openKolibri/klais-16/docs/char/074.jpg

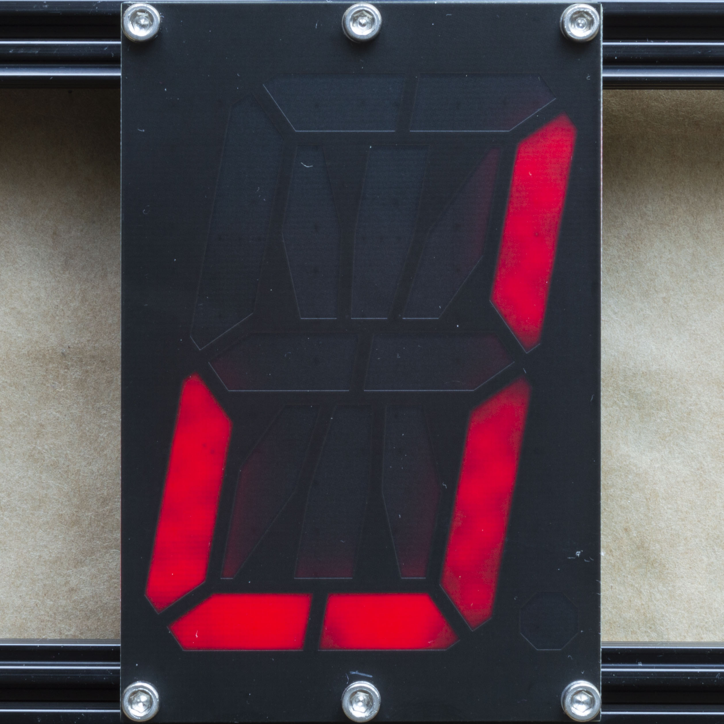
docs/char/074.jpg
