openKolibri/klais-16/docs/char/075.jpg

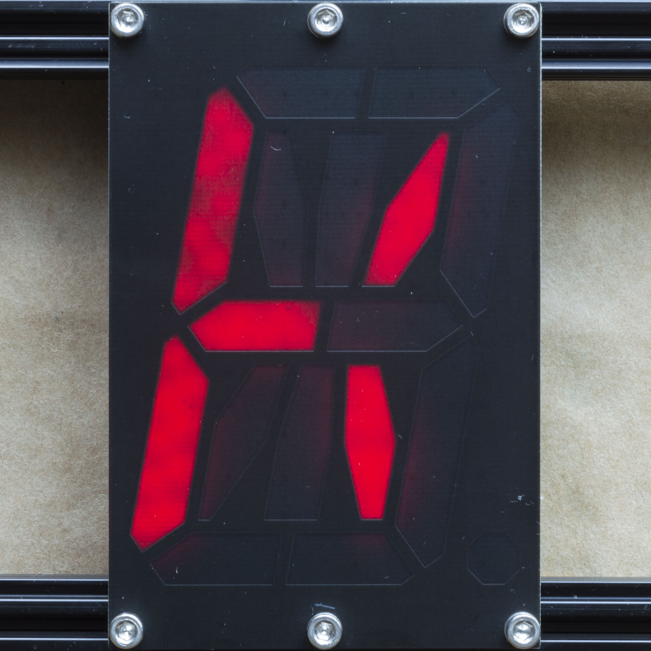
docs/char/075.jpg
