openKolibri/klais-16/docs/char/077.jpg

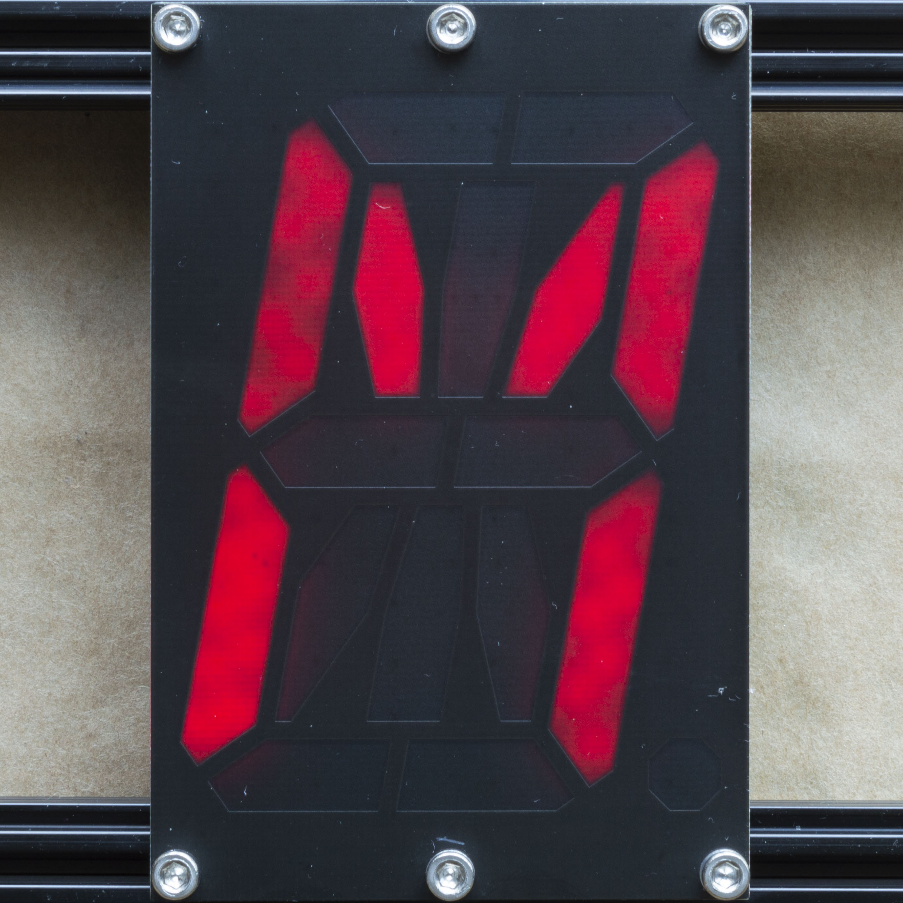
docs/char/077.jpg
