openKolibri/klais-16/docs/char/079.jpg

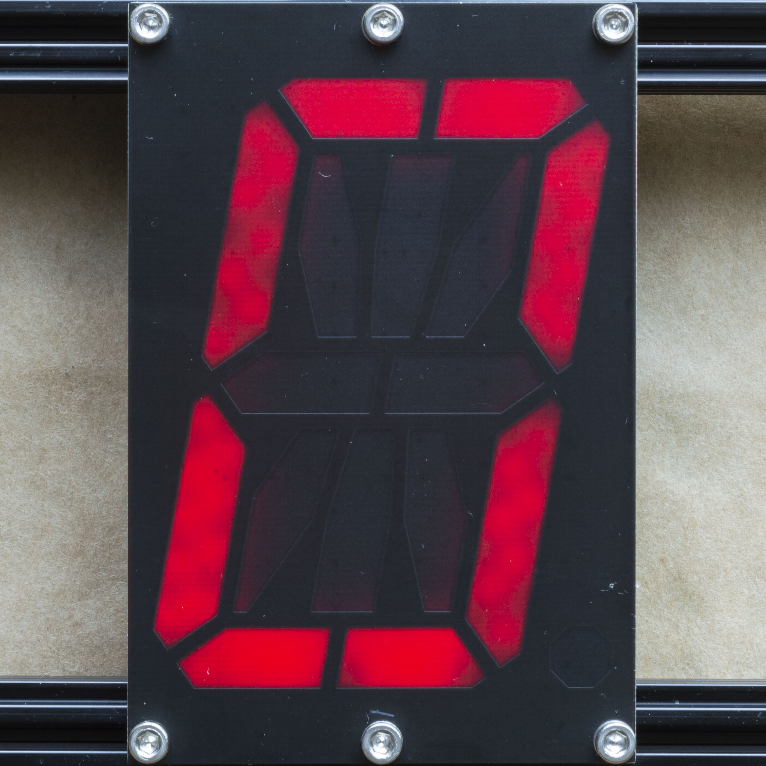
docs/char/079.jpg
