openKolibri/klais-16/docs/char/086.jpg

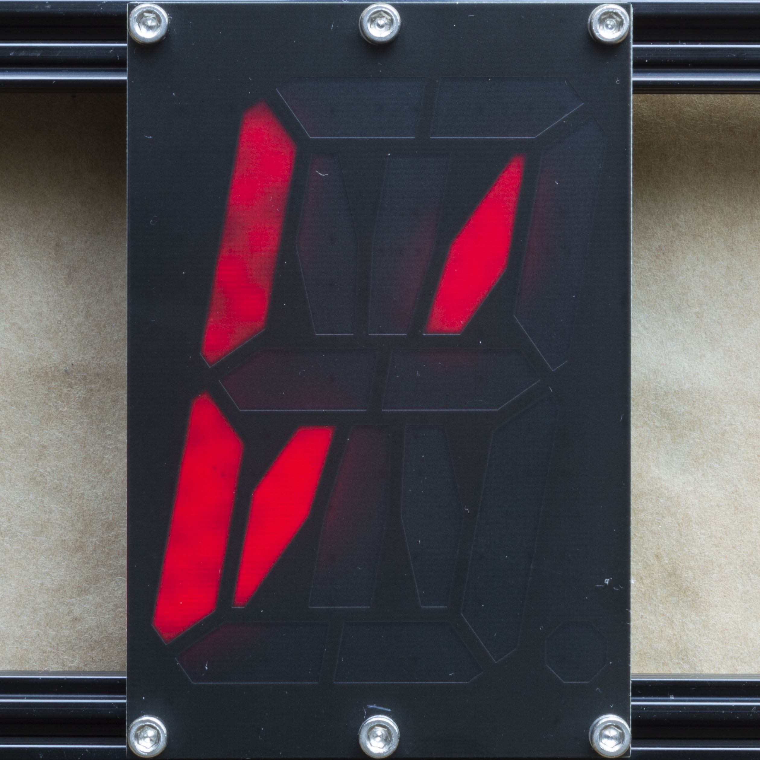
docs/char/086.jpg
