openKolibri/klais-16/docs/char/087.jpg

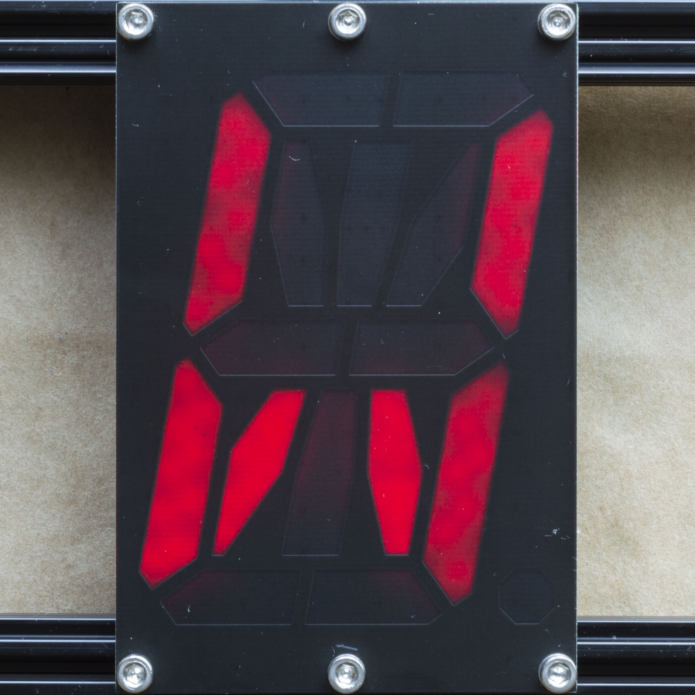
docs/char/087.jpg
