openKolibri/klais-16/docs/char/088.jpg

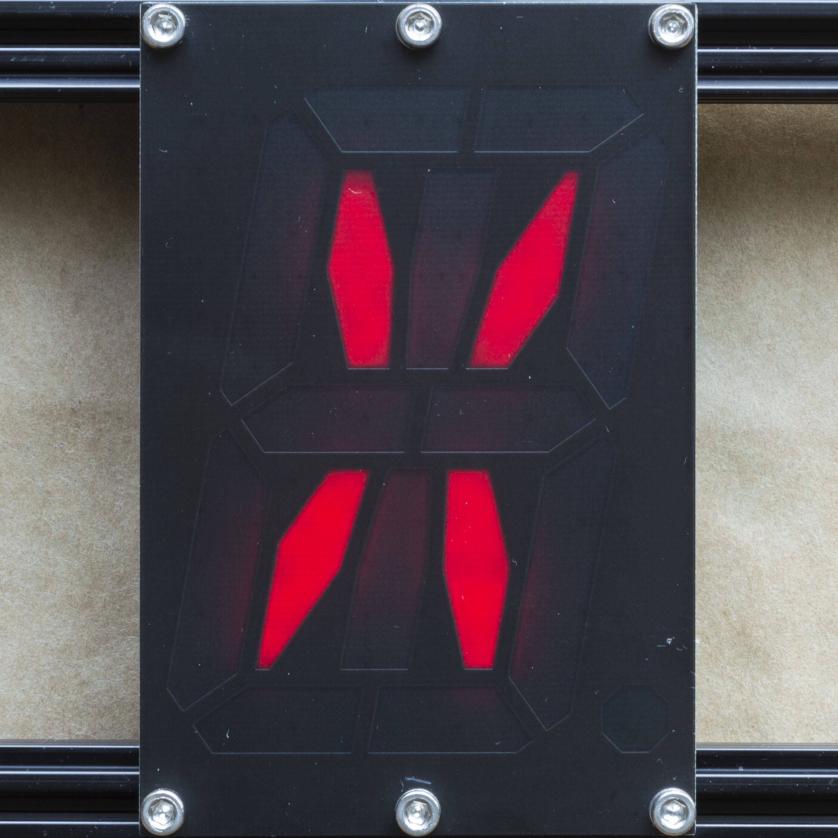
docs/char/088.jpg
