openKolibri/klais-16/docs/char/092.jpg

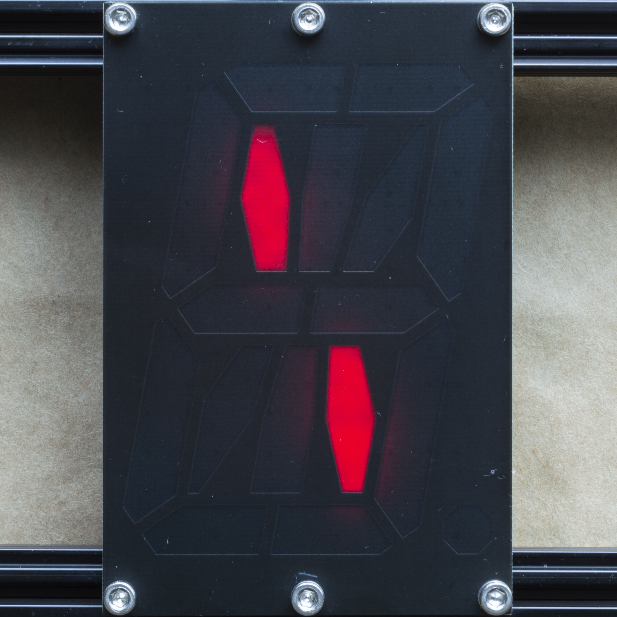
docs/char/092.jpg
