openKolibri/klais-16/docs/char/094.jpg

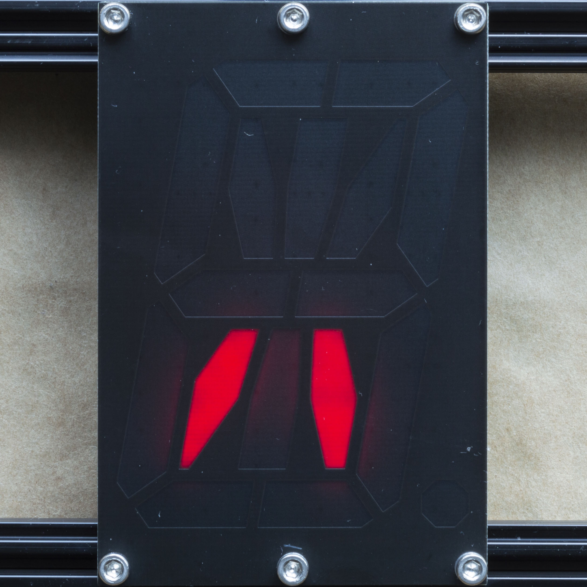
docs/char/094.jpg
