openKolibri/klais-16/docs/char/096.jpg

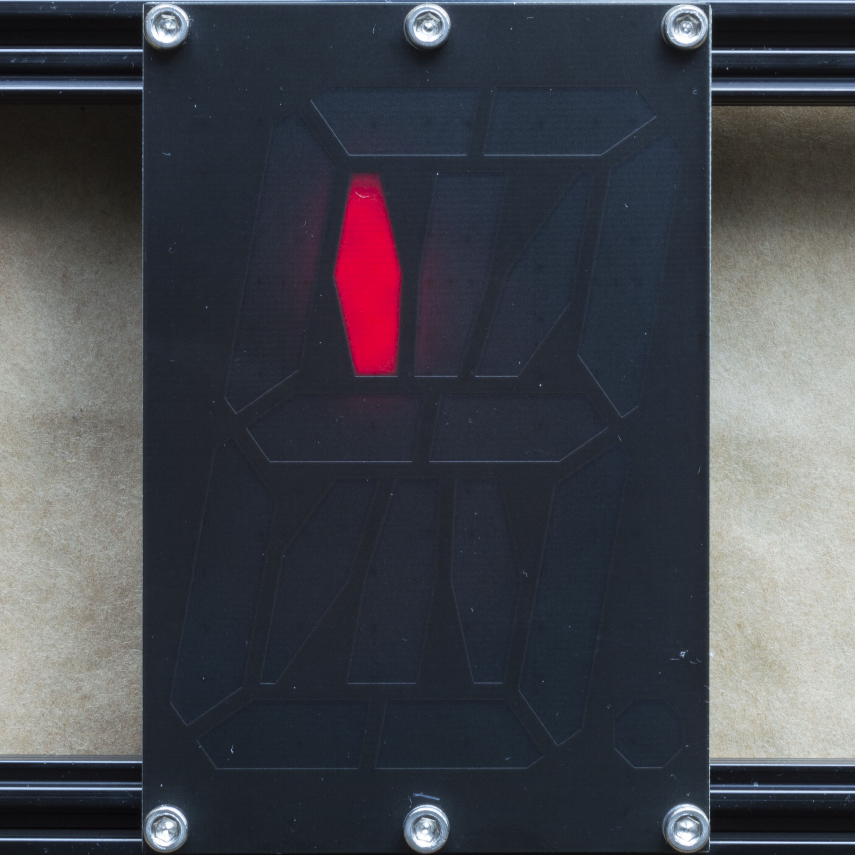
docs/char/096.jpg
