openKolibri/klais-16/docs/char/097.jpg

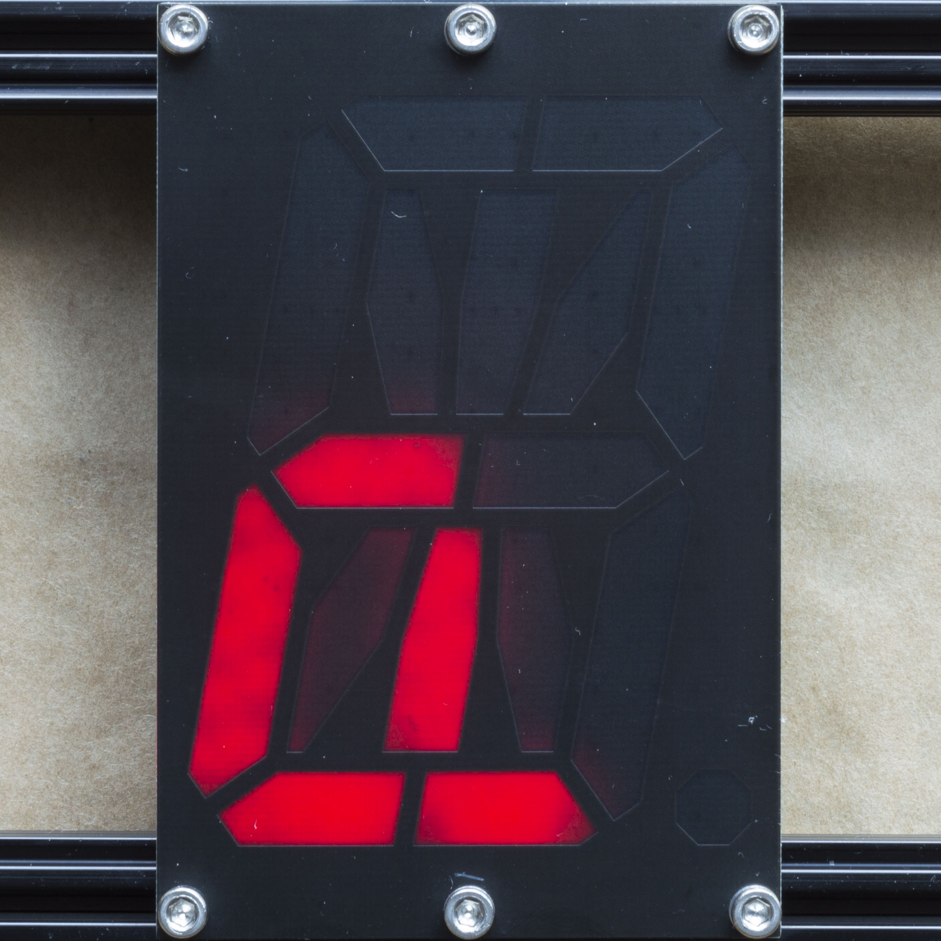
docs/char/097.jpg
