openKolibri/klais-16/docs/char/098.jpg

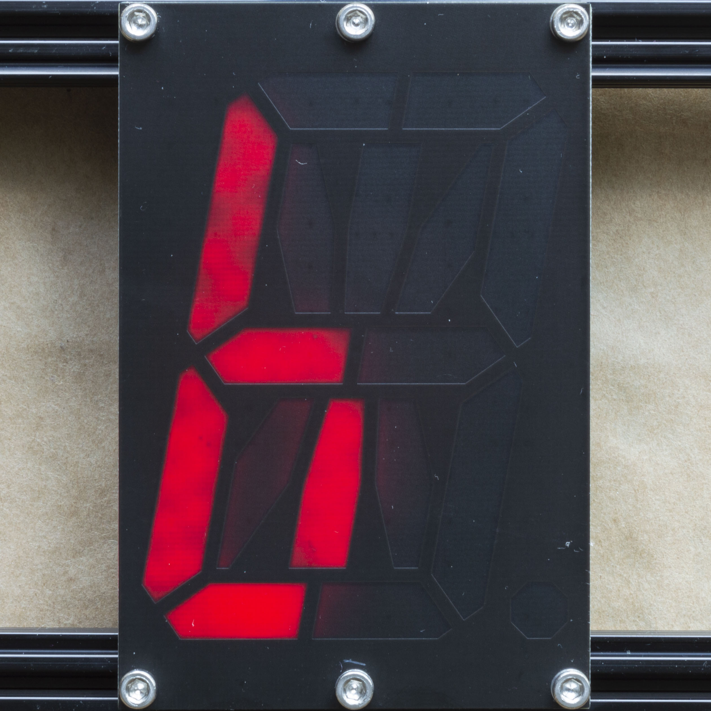
docs/char/098.jpg
