openKolibri/klais-16/docs/char/101.jpg

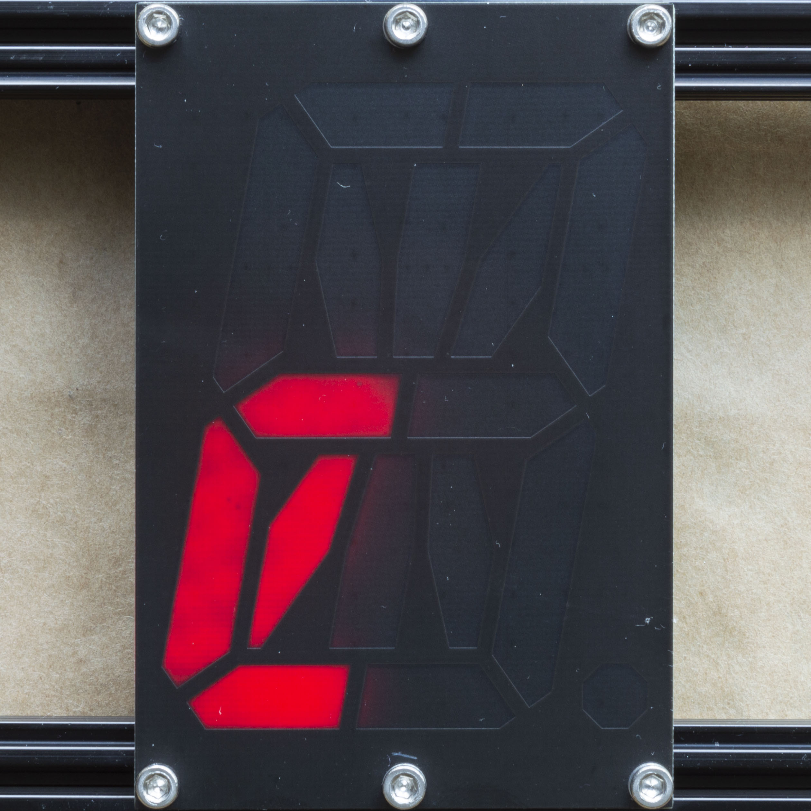
docs/char/101.jpg
