openKolibri/klais-16/docs/char/106.jpg

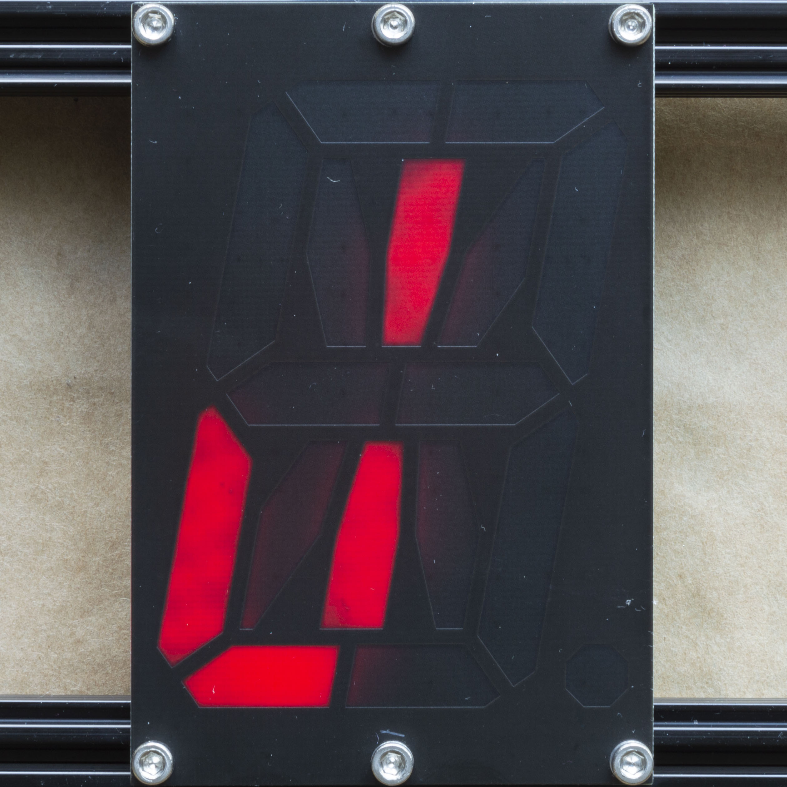
docs/char/106.jpg
