openKolibri/klais-16/docs/char/108.jpg

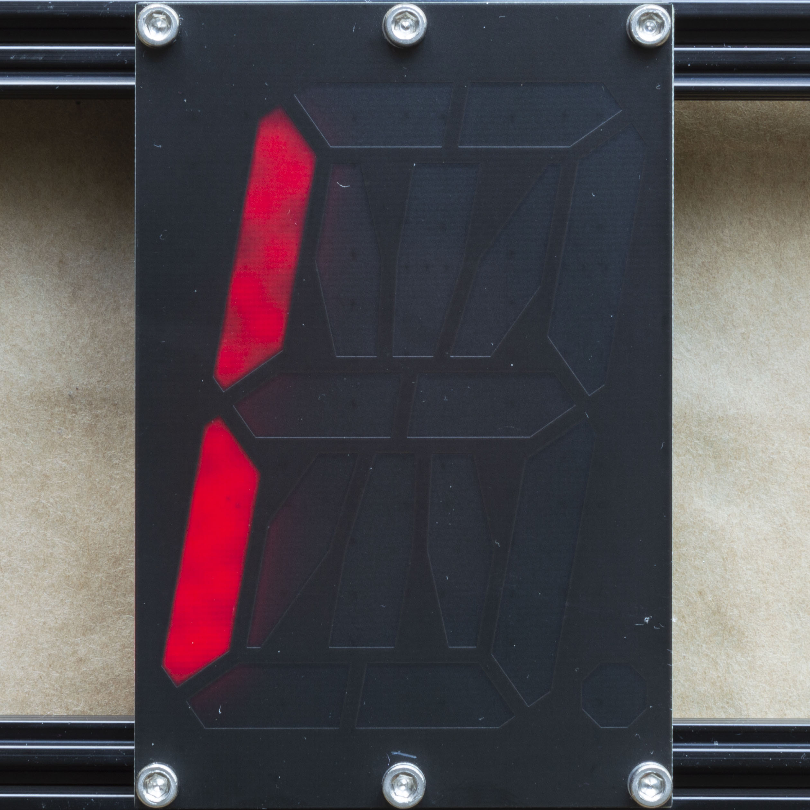
docs/char/108.jpg
