openKolibri/klais-16/docs/char/109.jpg

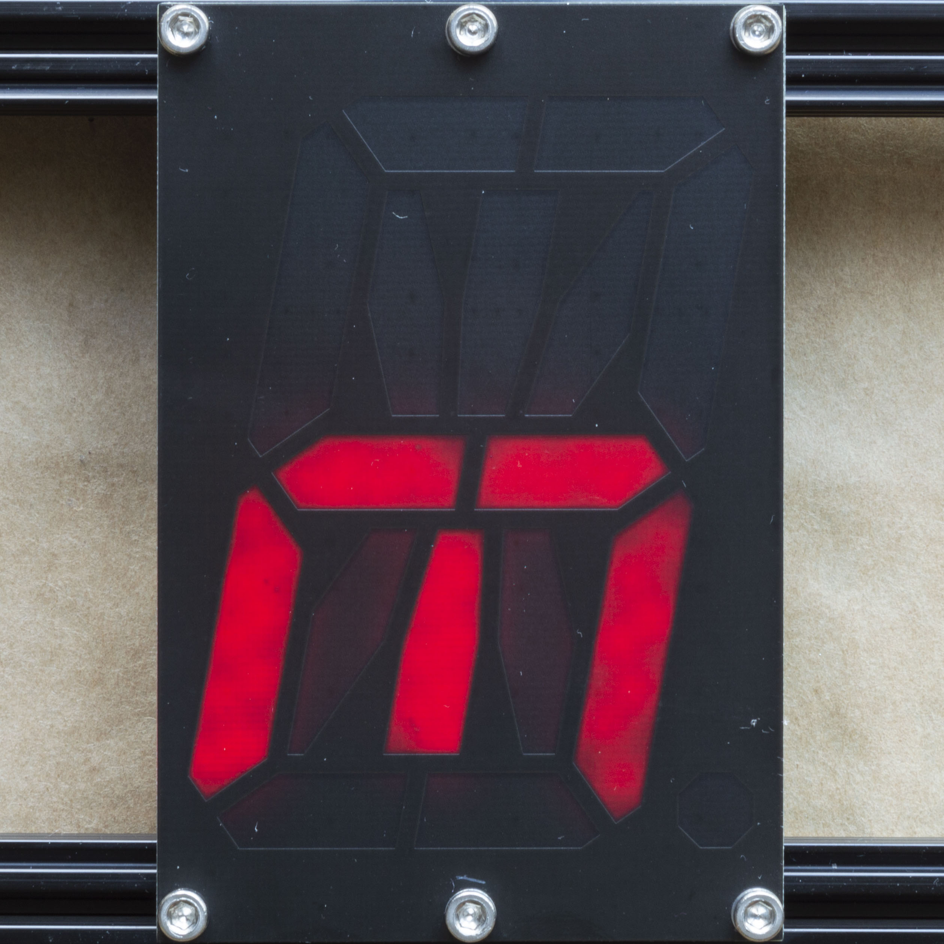
docs/char/109.jpg
