openKolibri/klais-16/docs/char/114.jpg

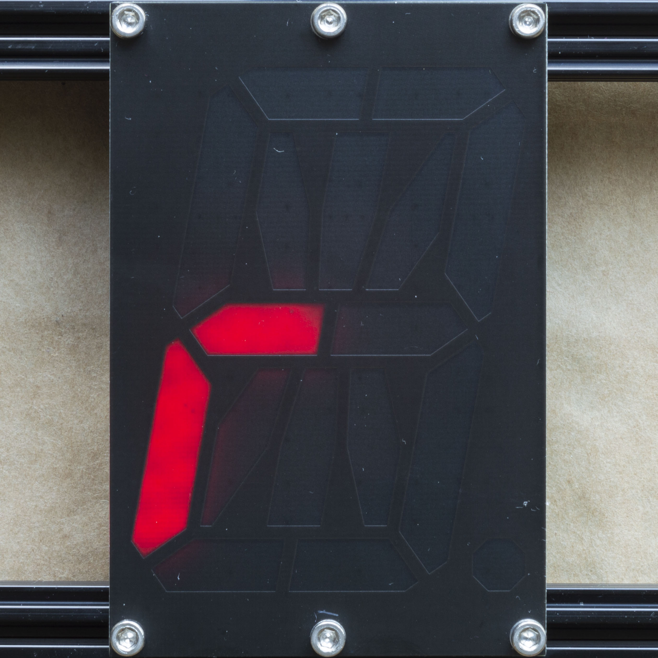
docs/char/114.jpg
