openKolibri/klais-16/docs/char/115.jpg

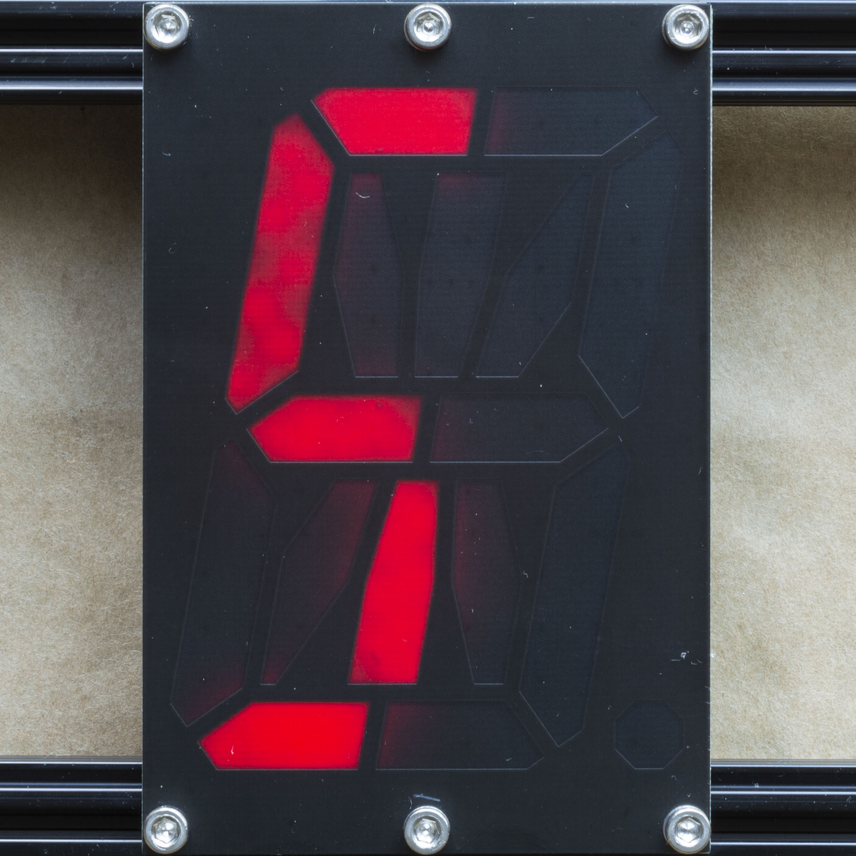
docs/char/115.jpg
