openKolibri/klais-16/docs/char/119.jpg

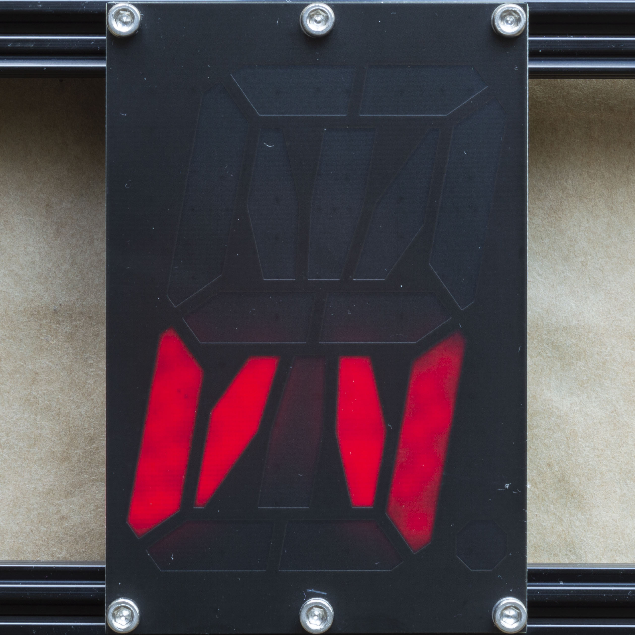
docs/char/119.jpg
