openKolibri/klais-16/docs/char/126.jpg

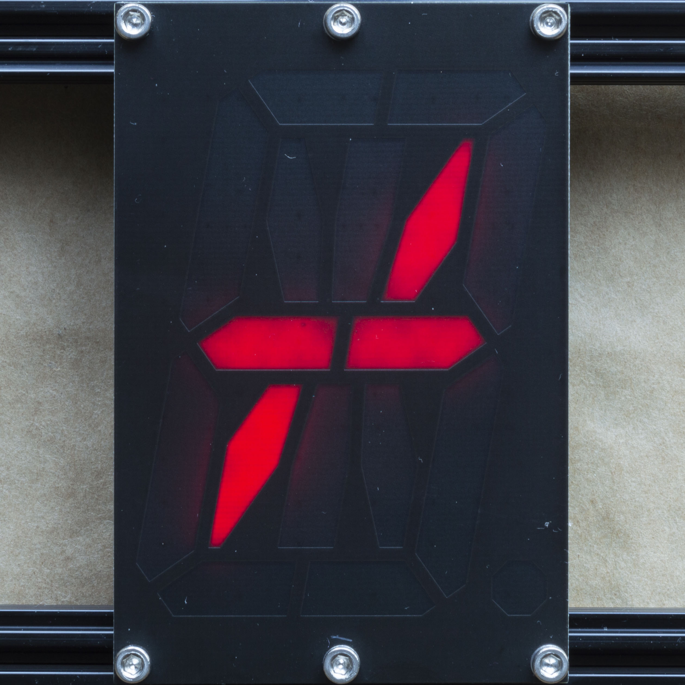
docs/char/126.jpg
