openKolibri/klais-16/docs/config/backPanel.jpg

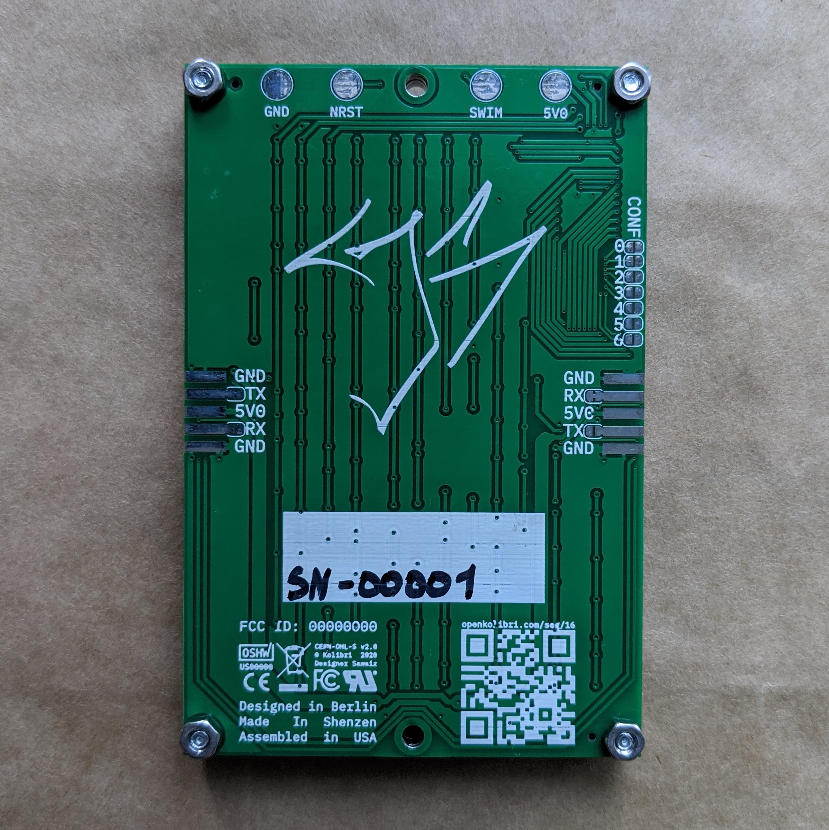
docs/config/backPanel.jpg
