openKolibri/klais-16/docs/config/config.jpg

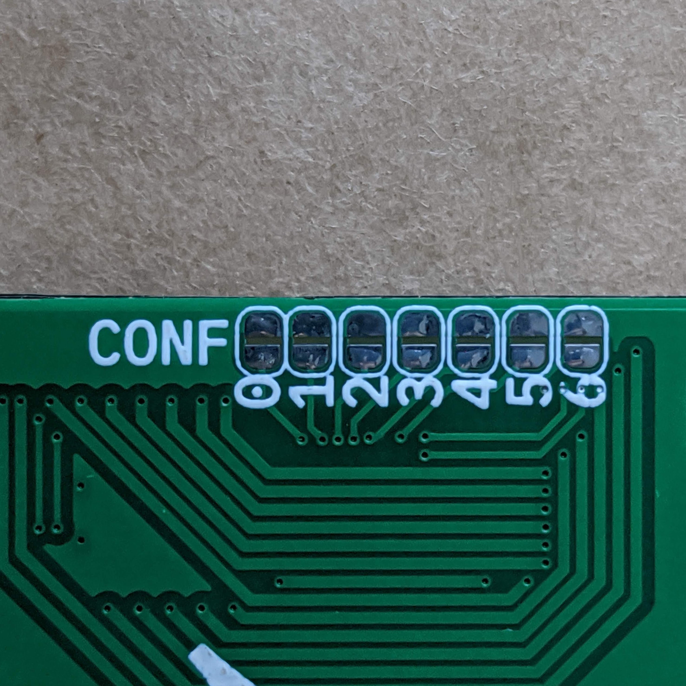
docs/config/config.jpg
