openKolibri/klais-16/docs/config/keyed.jpg

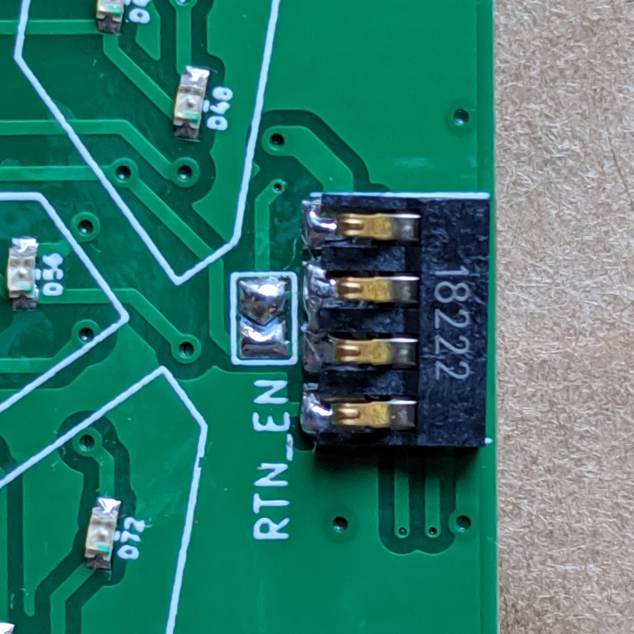
docs/config/keyed.jpg
