openKolibri/klais-16/docs/config/label.png

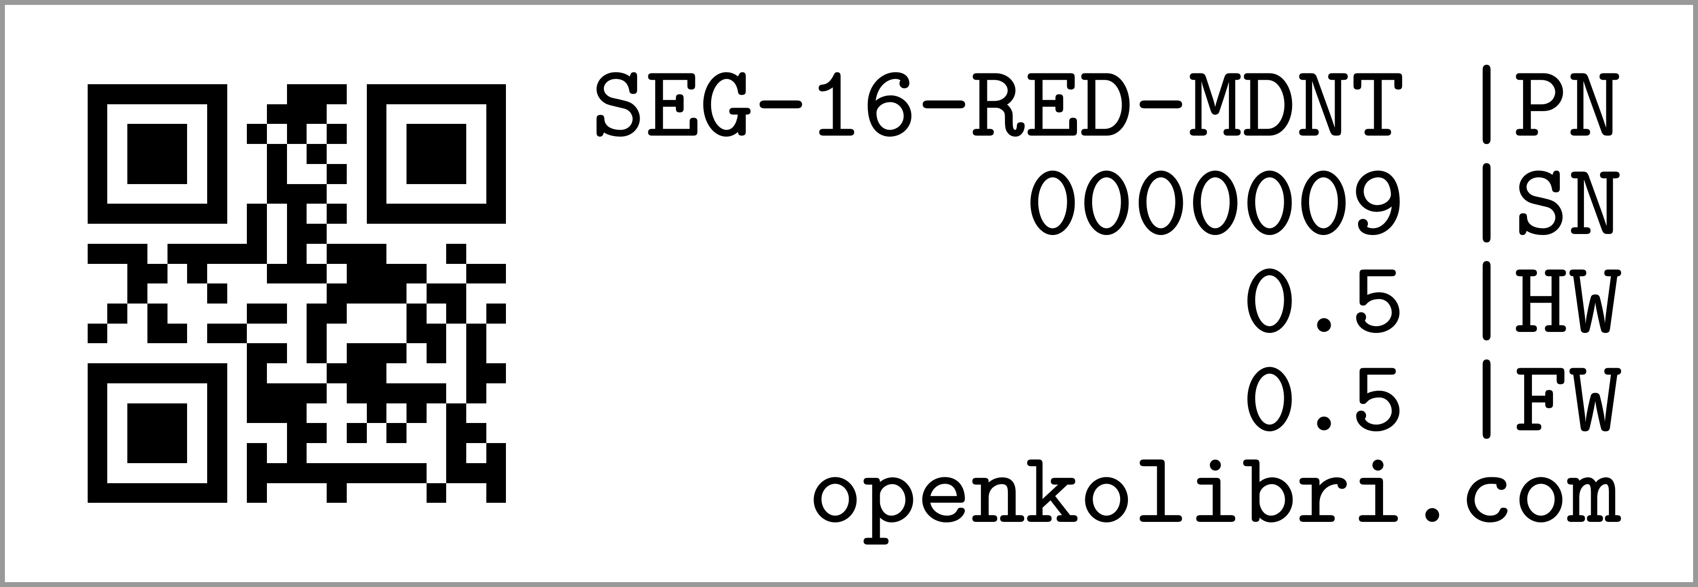
docs/config/label.png
