openKolibri/klais-16/docs/config/pgrm.jpg

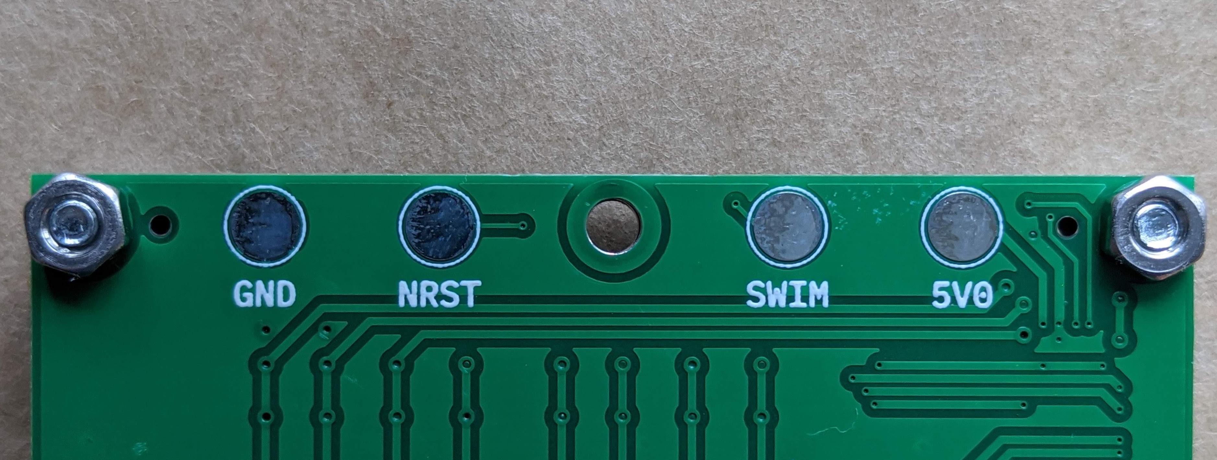
docs/config/pgrm.jpg
