openKolibri/klais-16/docs/firmware/dataCapImg.png

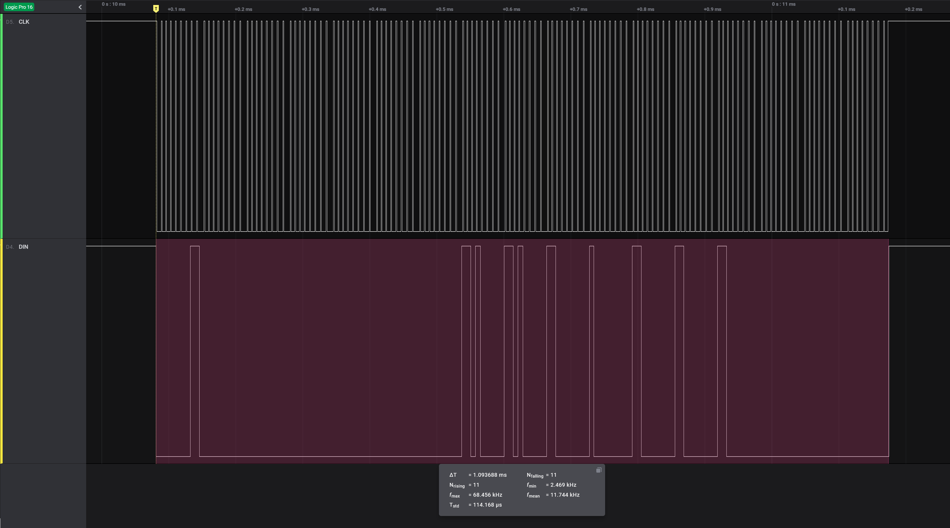
docs/firmware/dataCapImg.png
