openKolibri/klais-16/docs/firmware/segmentMap.png

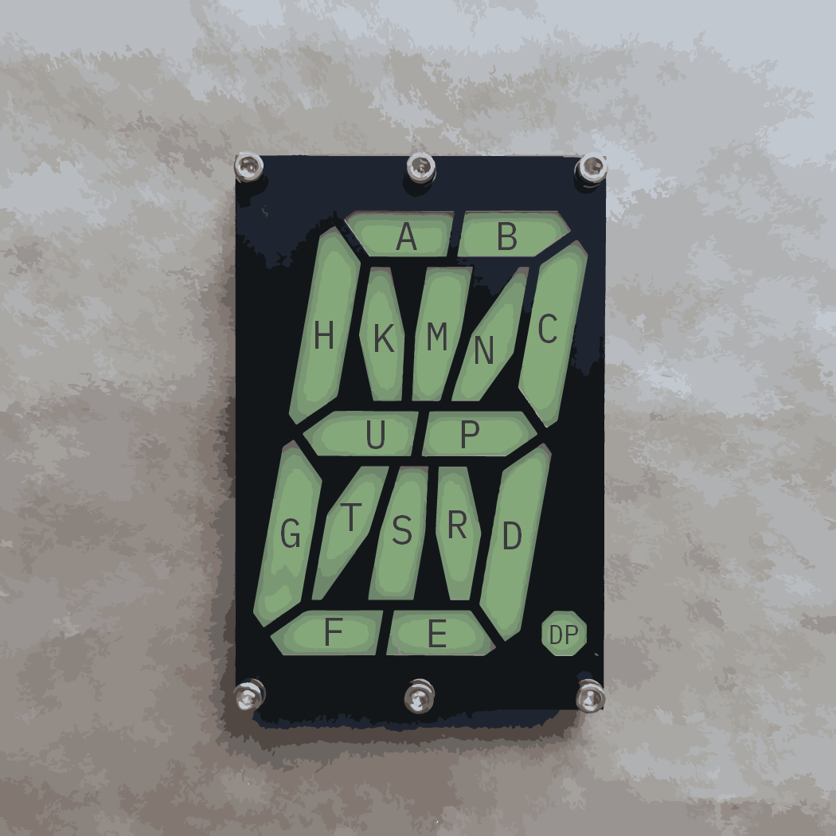
docs/firmware/segmentMap.png
