openKolibri/klais-16/docs/firmware/TM1640Timing.png

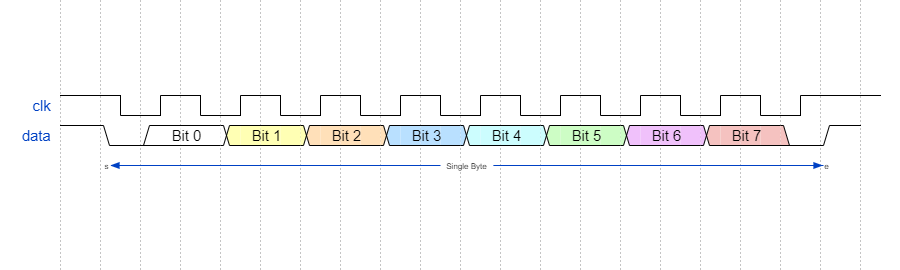
docs/firmware/TM1640Timing.png
