openKolibri/klais-16/docs/mounting/2020Extrusion.jpg

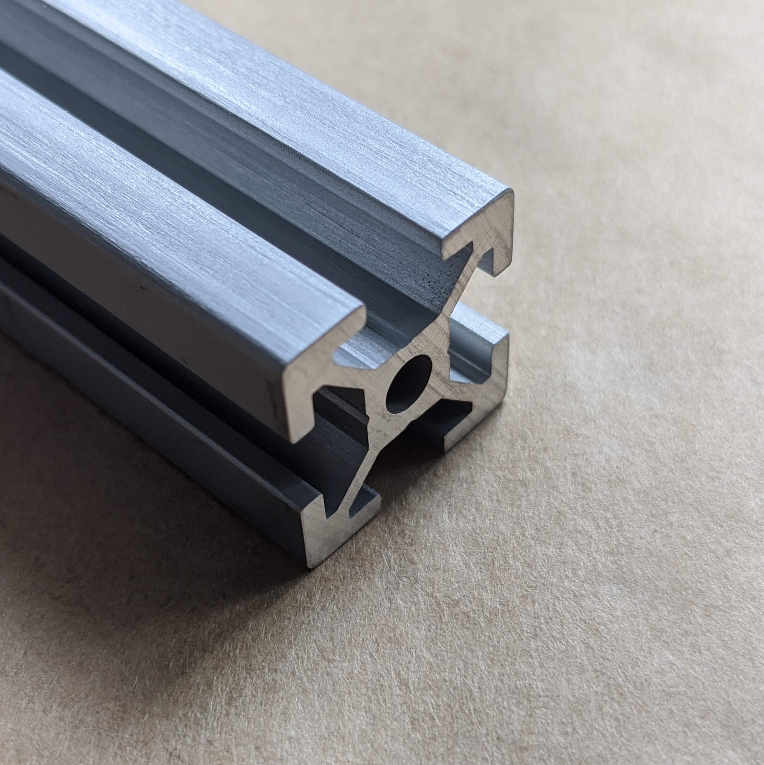
docs/mounting/2020Extrusion.jpg
