openKolibri/klais-16/docs/mounting/M3x8.jpg

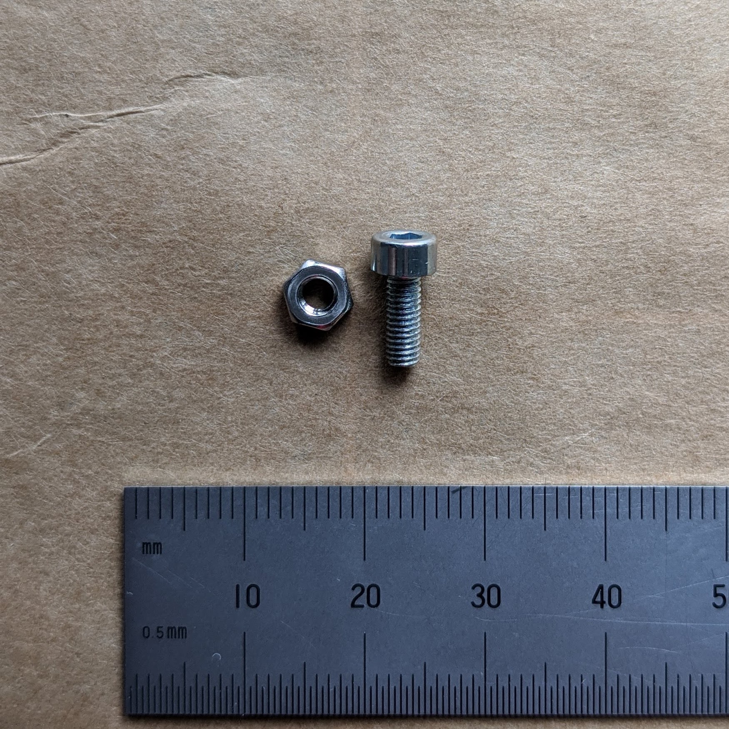
docs/mounting/M3x8.jpg
