openKolibri/klais-16/docs/mounting/mountingDim.png

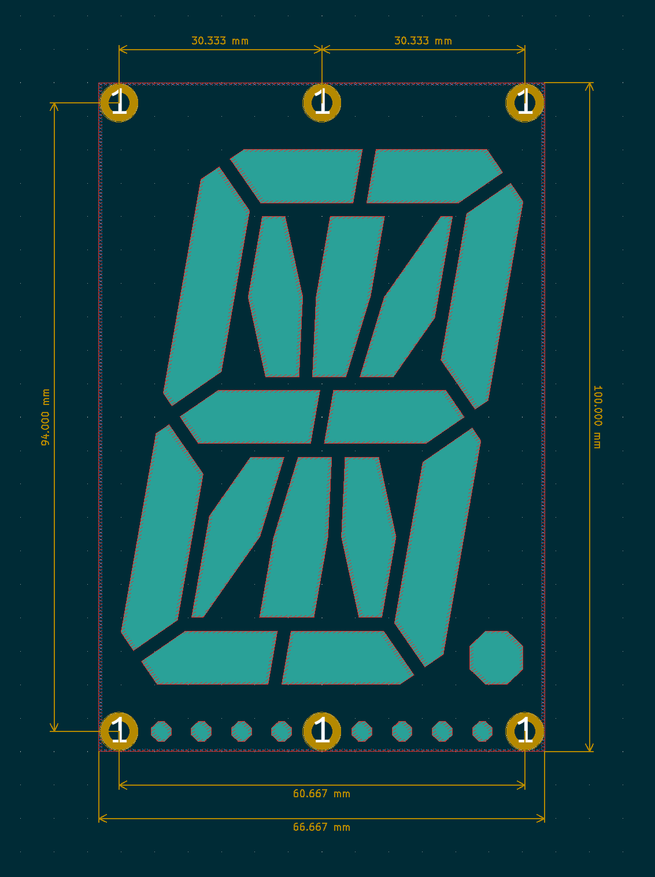
docs/mounting/mountingDim.png
