openKolibri/klais-16/docs/mounting/R3075.jpg

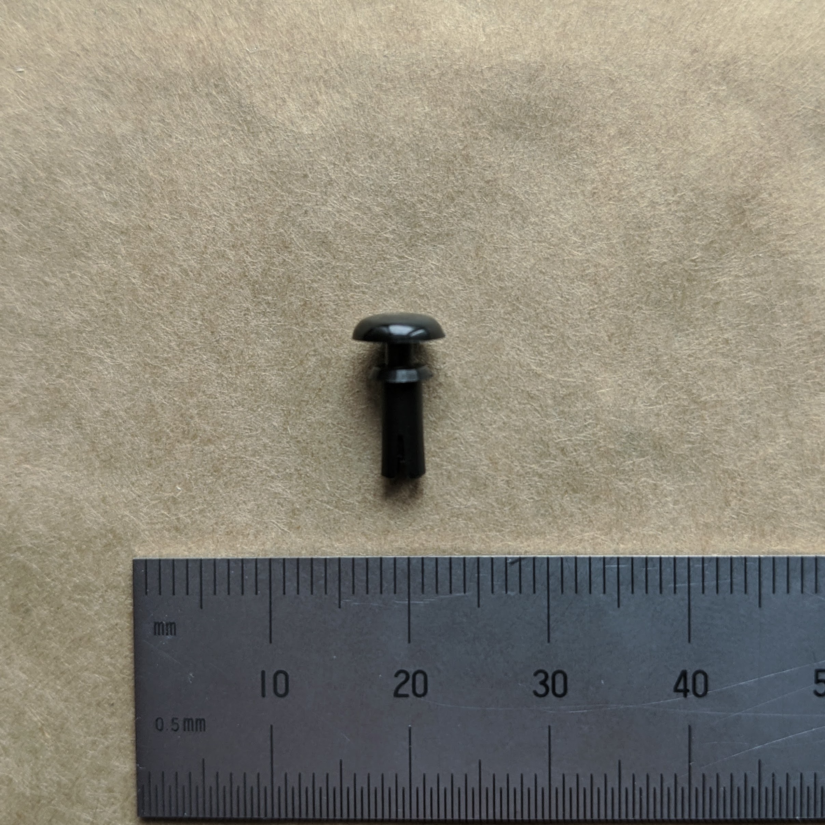
docs/mounting/R3075.jpg
