openKolibri/klais-16/docs/mounting/springPin.jpg

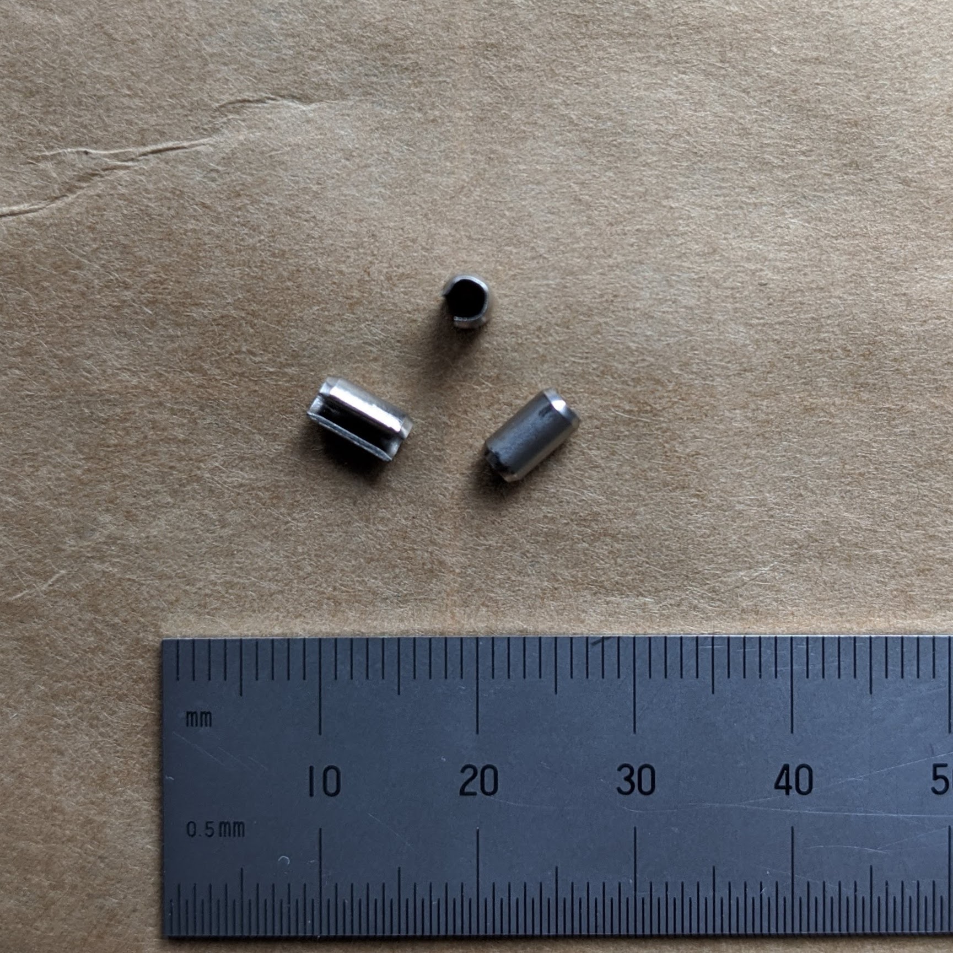
docs/mounting/springPin.jpg
