openKolibri/klais-16/docs/product/isoArray.jpg

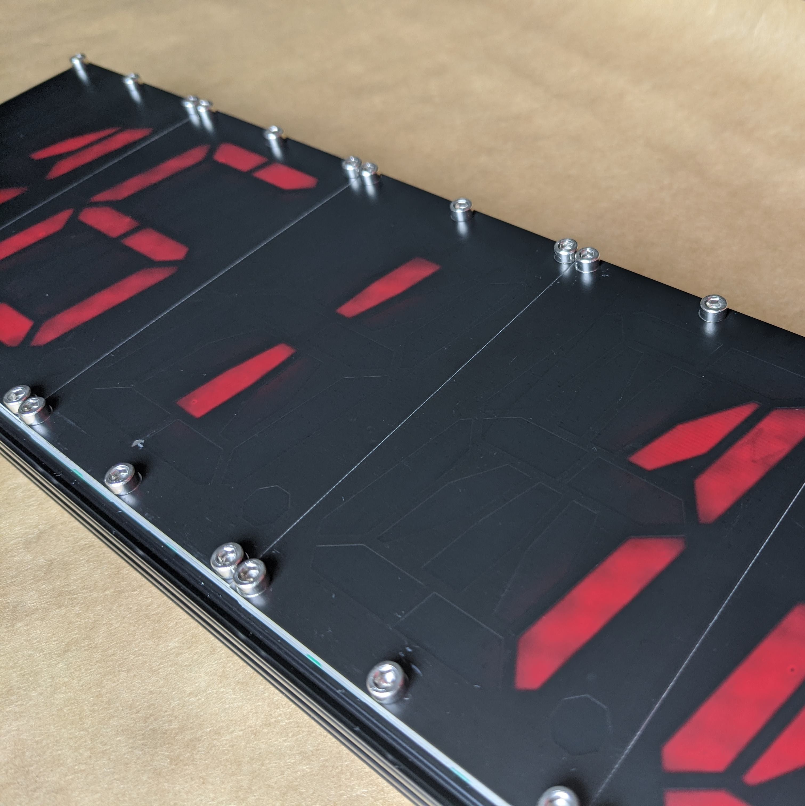
docs/product/isoArray.jpg
