openKolibri/klais-16/docs/programmer/minimalProgrammer-render.png

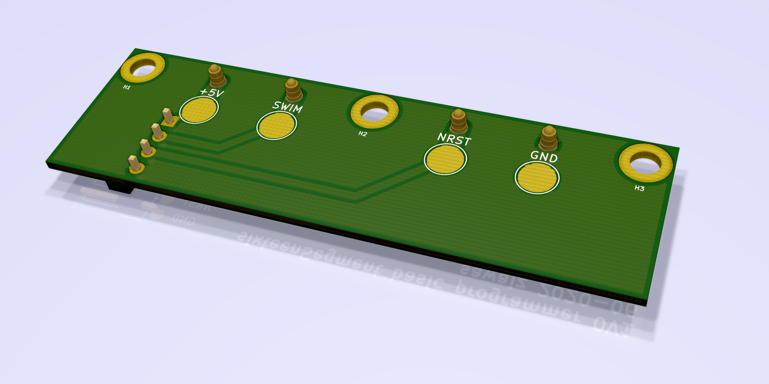
docs/programmer/minimalProgrammer-render.png
