openKolibri/klais-16/docs/title/DISPLAY.png

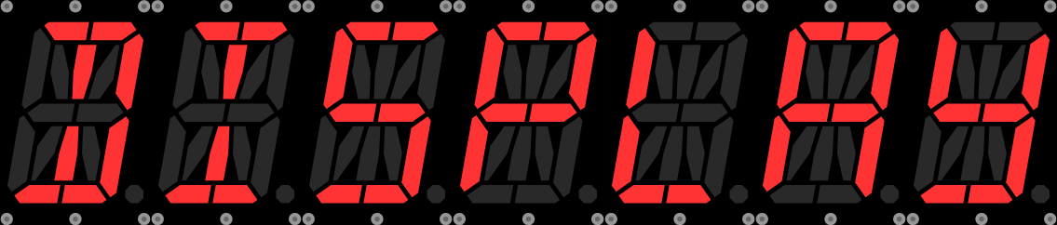
docs/title/DISPLAY.png
