openKolibri/klais-16/docs/title/SEGMENT.png

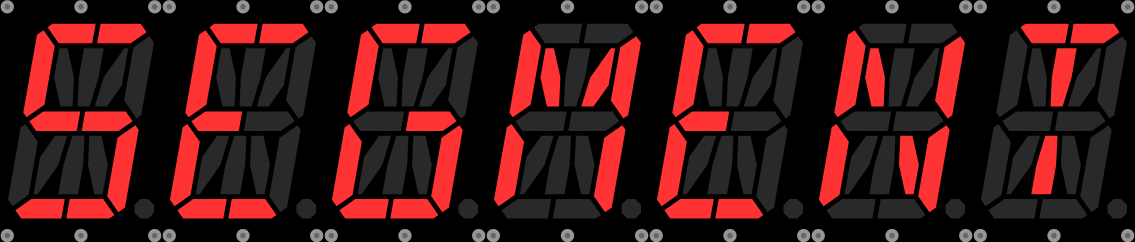
docs/title/SEGMENT.png
