openKolibri/klais-16/docs/title/SIXTEEN.png

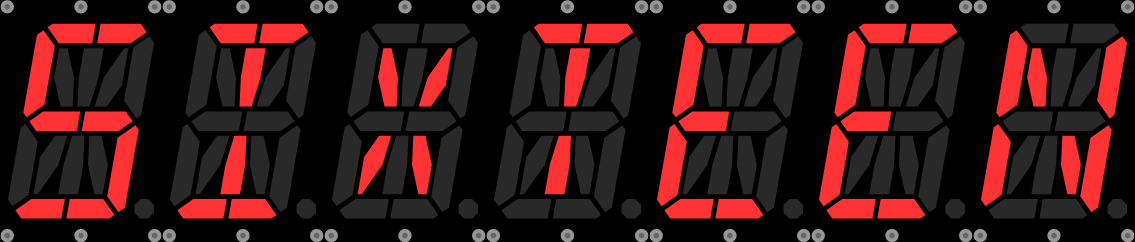
docs/title/SIXTEEN.png
