openKolibri/klais-16/pcb/SEG-16-XXX-XXXX-L0/components/0472861001/0472861001.jpg

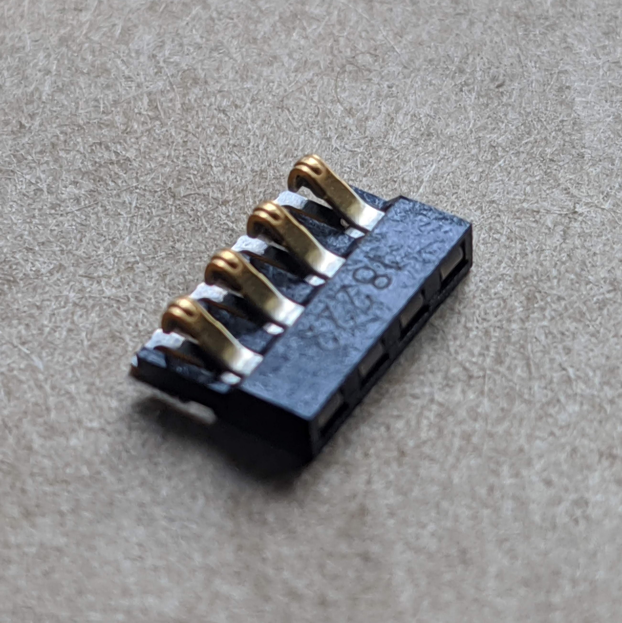
pcb/SEG-16-XXX-XXXX-L0/components/0472861001/0472861001.jpg
