openKolibri/klais-16/pcb/SEG-16-XXX-XXXX-L0/components/KT-0603R/KT-0603R.jpg

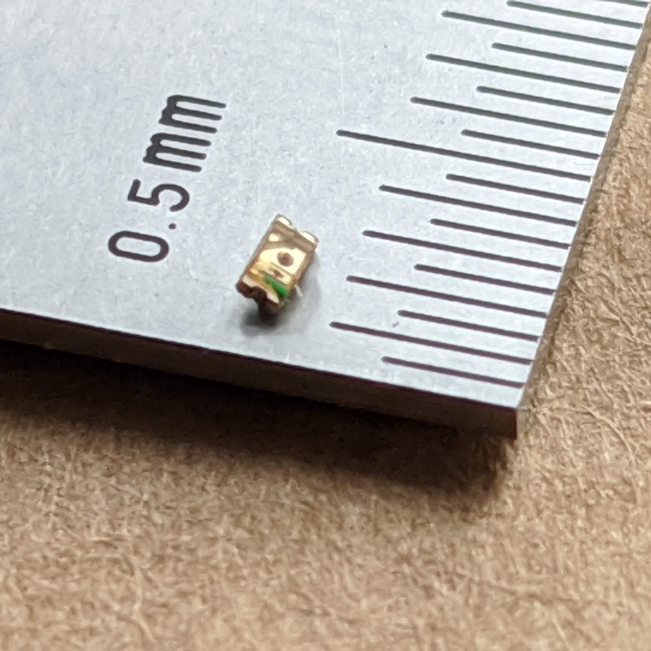
pcb/SEG-16-XXX-XXXX-L0/components/KT-0603R/KT-0603R.jpg
