openKolibri/klais-16/pcb/SEG-16-XXX-XXXX-L0/components/markings/bmp/FCC.bmp

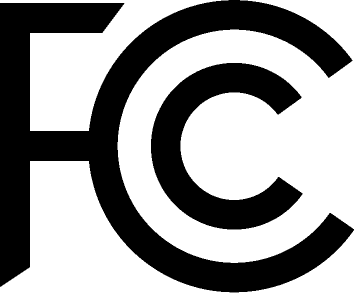
pcb/SEG-16-XXX-XXXX-L0/components/markings/bmp/FCC.bmp
