openKolibri/klais-16/pcb/SEG-16-XXX-XXXX-L0/components/markings/bmp/FCCID.bmp

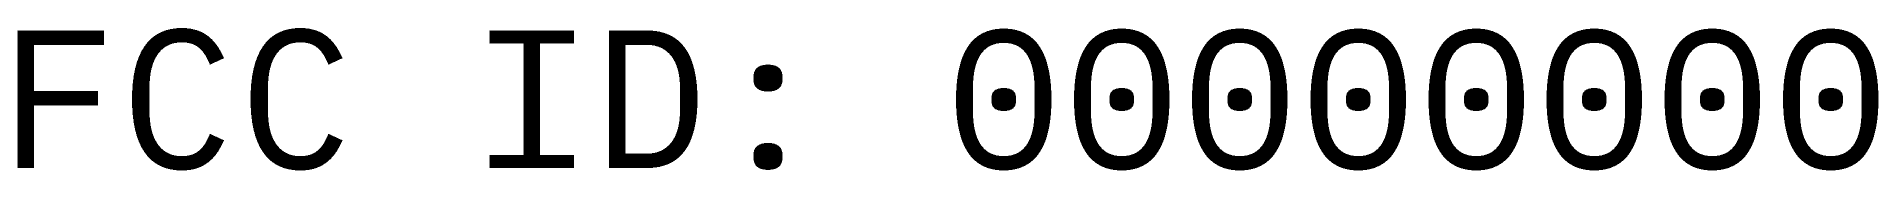
pcb/SEG-16-XXX-XXXX-L0/components/markings/bmp/FCCID.bmp
