openKolibri/klais-16/pcb/SEG-16-XXX-XXXX-L0/components/markings/bmp/SEG-16-QR-Lone.bmp

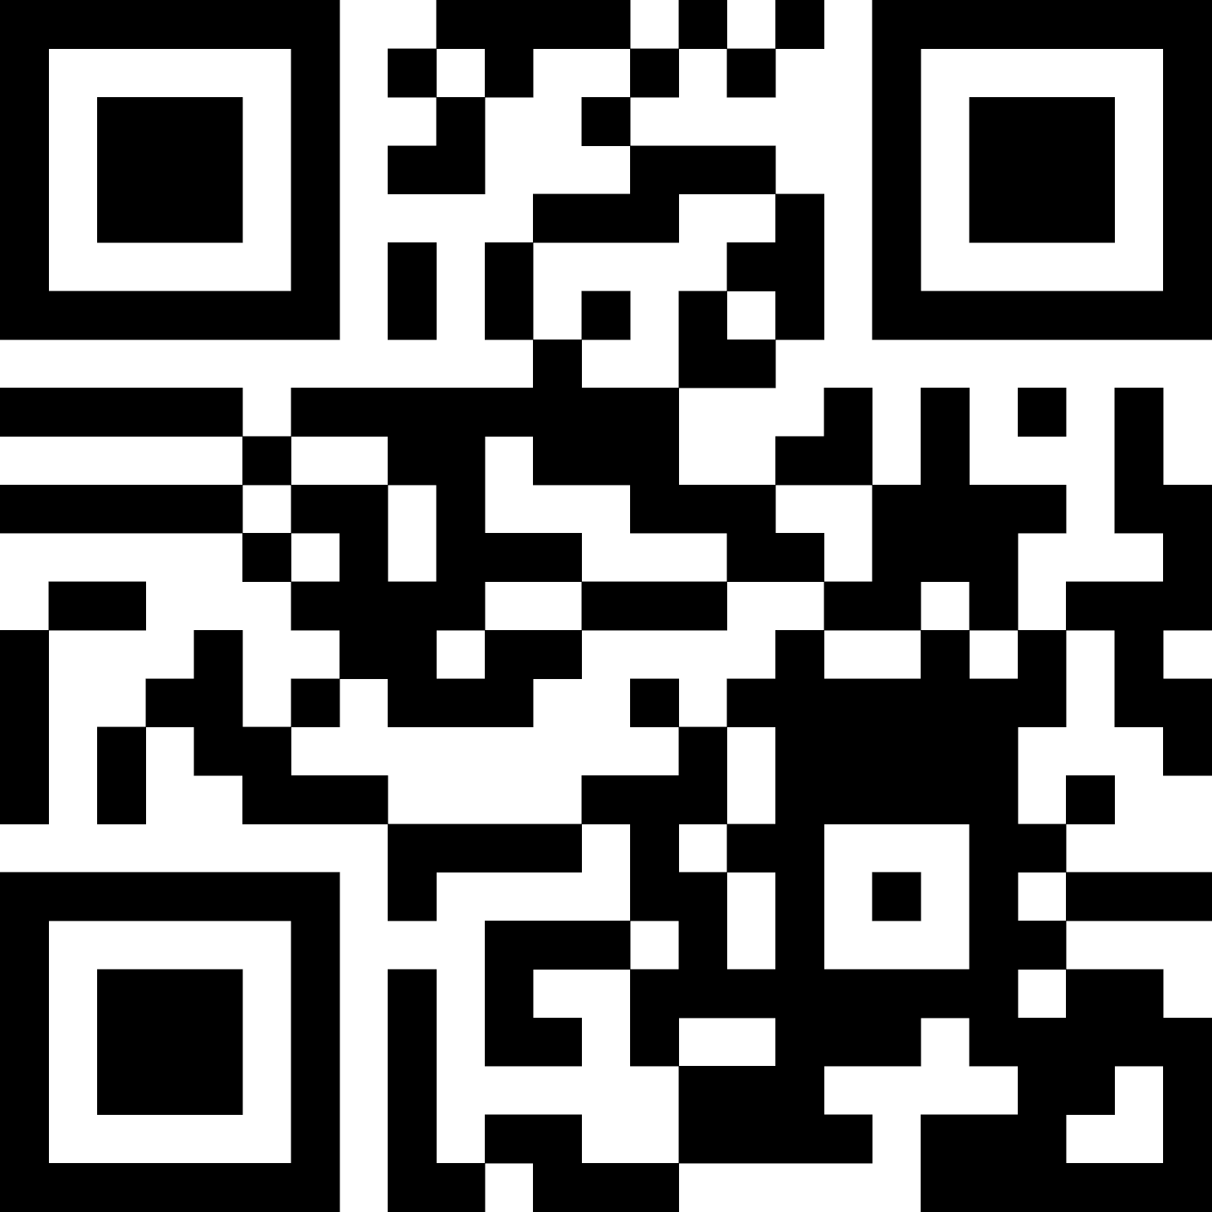
pcb/SEG-16-XXX-XXXX-L0/components/markings/bmp/SEG-16-QR-Lone.bmp
