openKolibri/klais-16/pcb/SEG-16-XXX-XXXX-L0/components/STM8S003/STM8S003.jpg

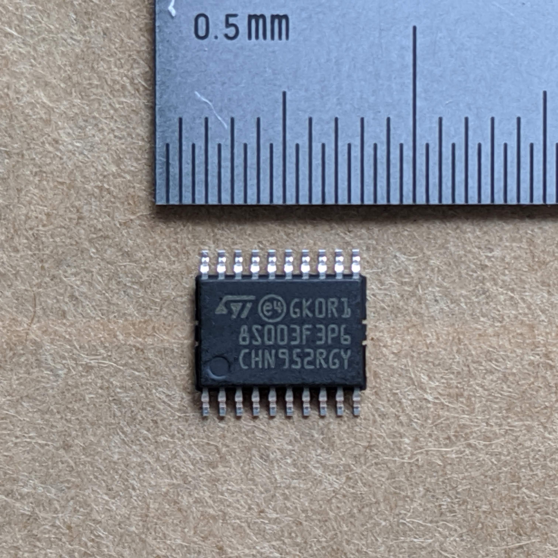
pcb/SEG-16-XXX-XXXX-L0/components/STM8S003/STM8S003.jpg
