openKolibri/klais-16/pcb/SEG-16-XXX-XXXX-L0/components/TAJA106K016RNJ/TAJA106K016RNJ.jpg

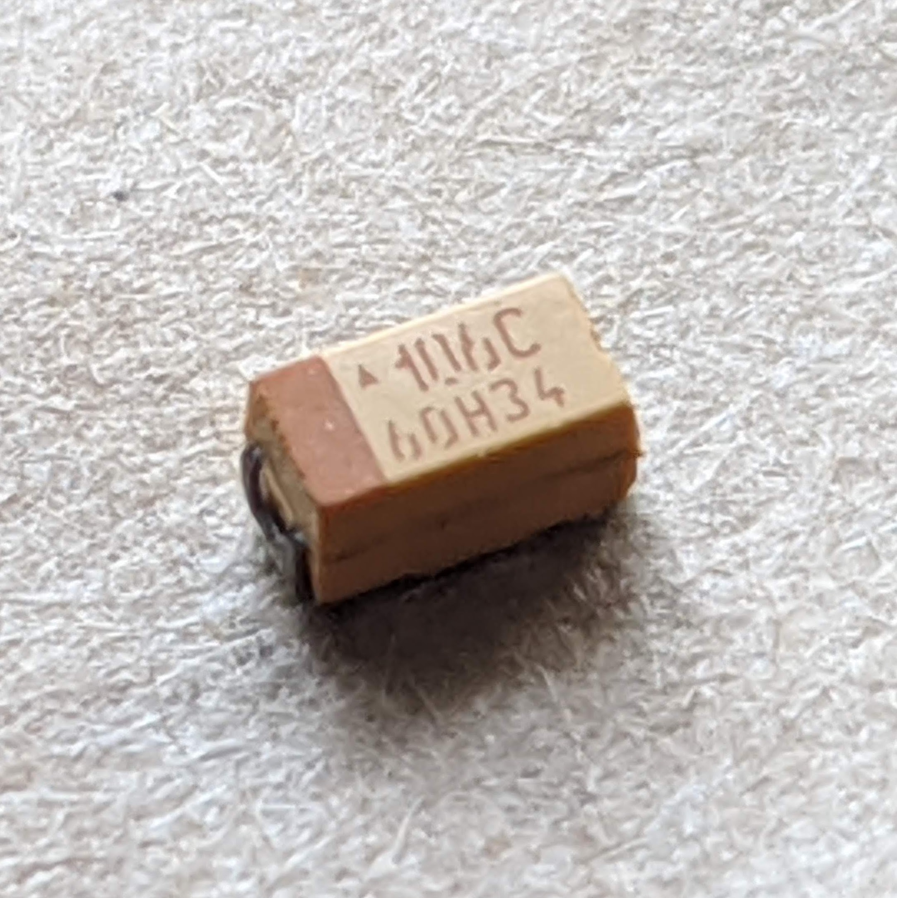
pcb/SEG-16-XXX-XXXX-L0/components/TAJA106K016RNJ/TAJA106K016RNJ.jpg
