openKolibri/klais-16/pcb/SEG-16-XXX-XXXX-L0/components/TM1640/TM1640.jpg

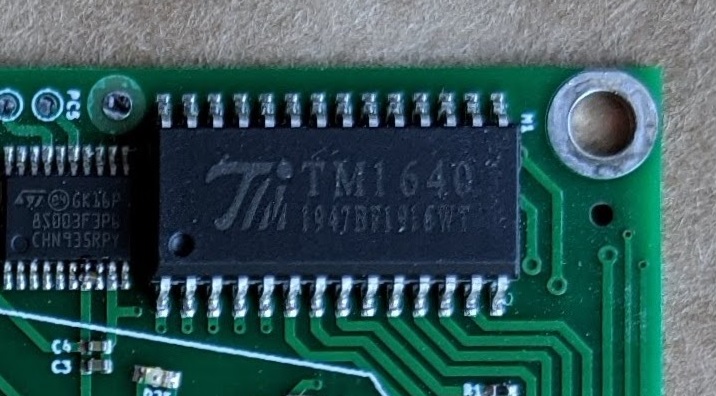
pcb/SEG-16-XXX-XXXX-L0/components/TM1640/TM1640.jpg
