openKolibri/klais-16/pcb/SEG-16-XXX-XXXX-L1/components/TAJB107K006RNJ/TAJB107K006RNJ.jpg

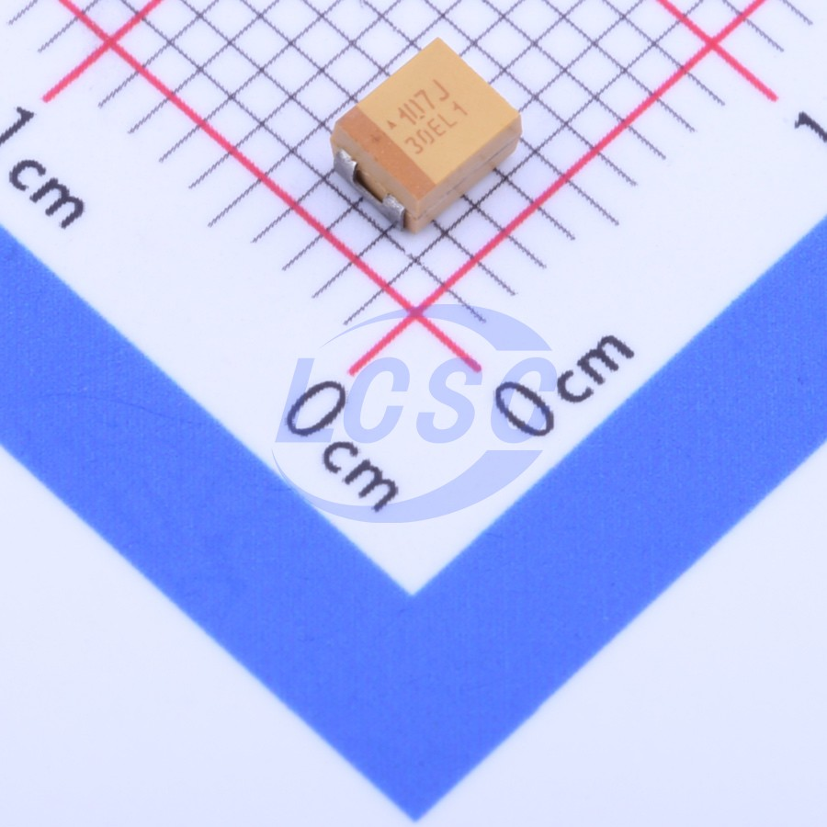
pcb/SEG-16-XXX-XXXX-L1/components/TAJB107K006RNJ/TAJB107K006RNJ.jpg
