openKolibri/klais-16/docs/assembly/assembly.png

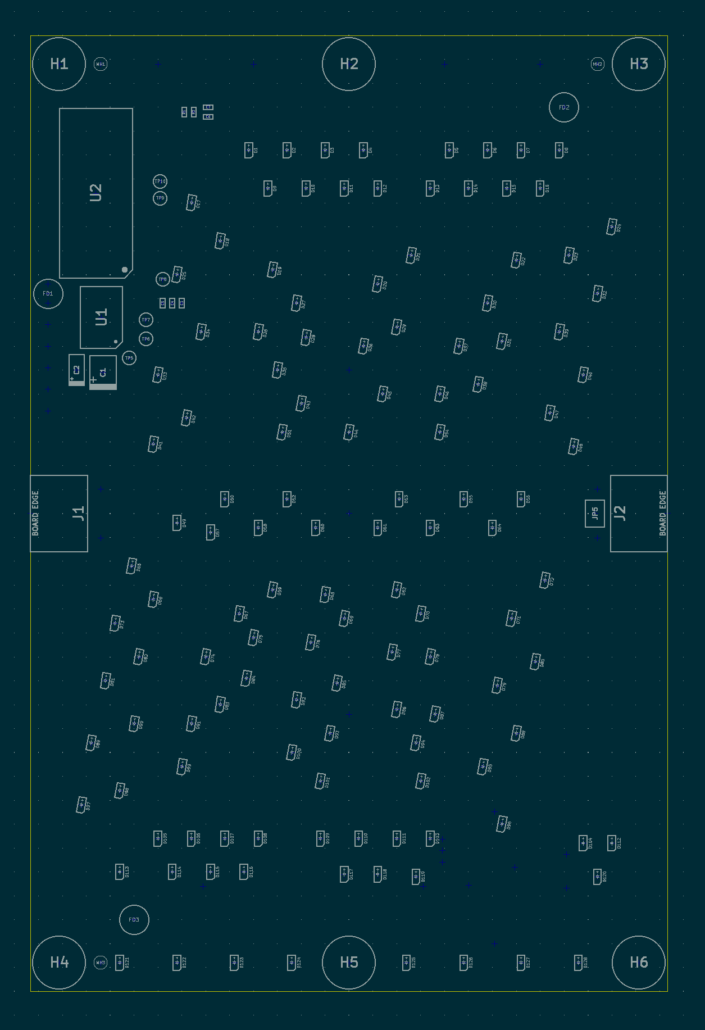
docs/assembly/assembly.png
