openKolibri/klais-16/docs/assembly/imProto.png

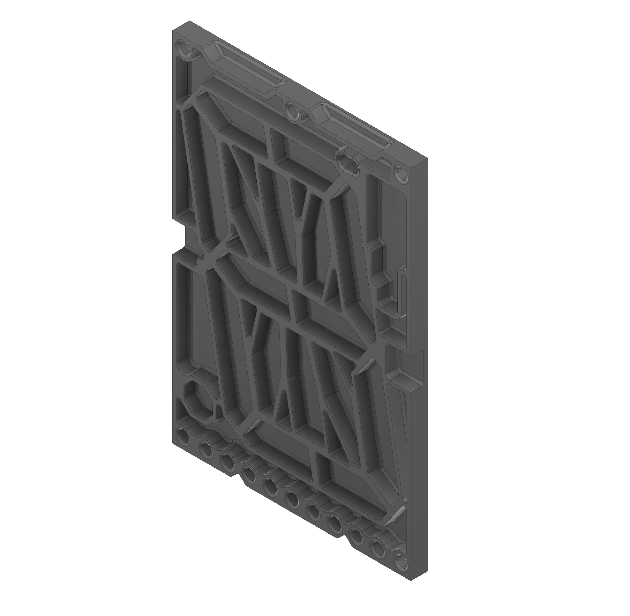
docs/assembly/imProto.png
