openKolibri/klais-16/docs/assembly/L0.png

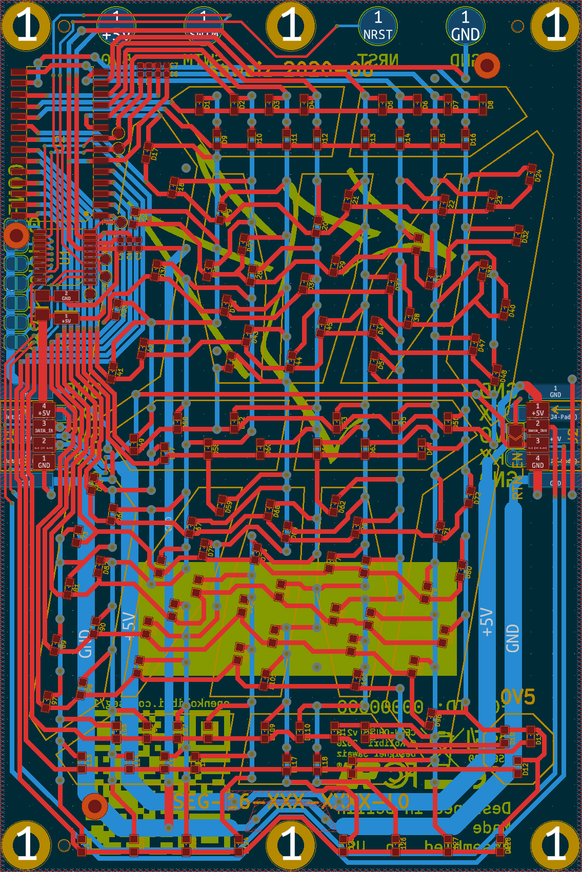
docs/assembly/L0.png
