openKolibri/klais-16/docs/assembly/L1-DIE.png

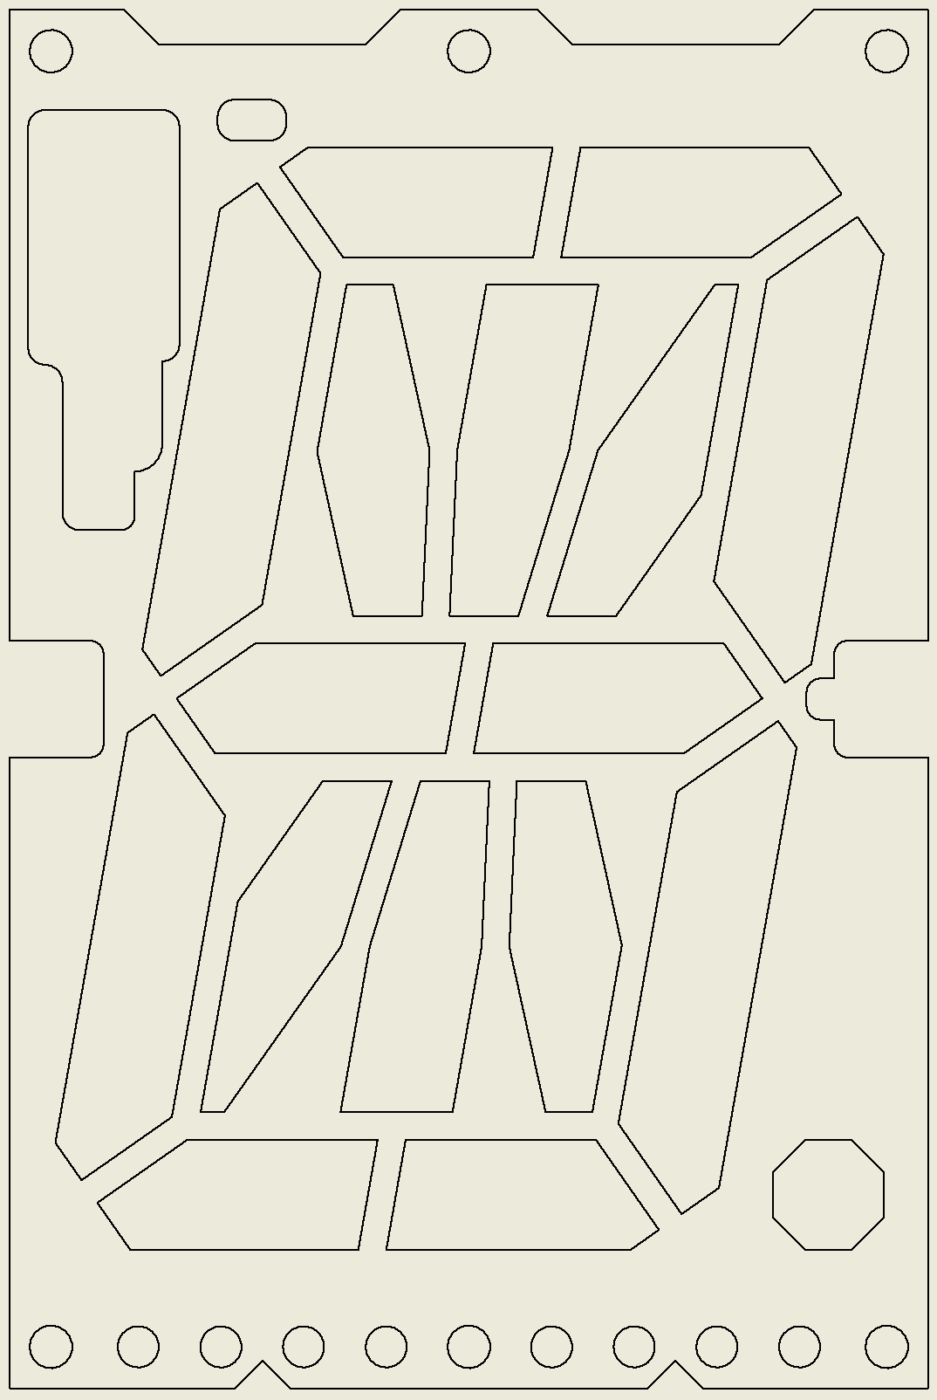
docs/assembly/L1-DIE.png
