openKolibri/klais-16/docs/assembly/L3-DIE.png

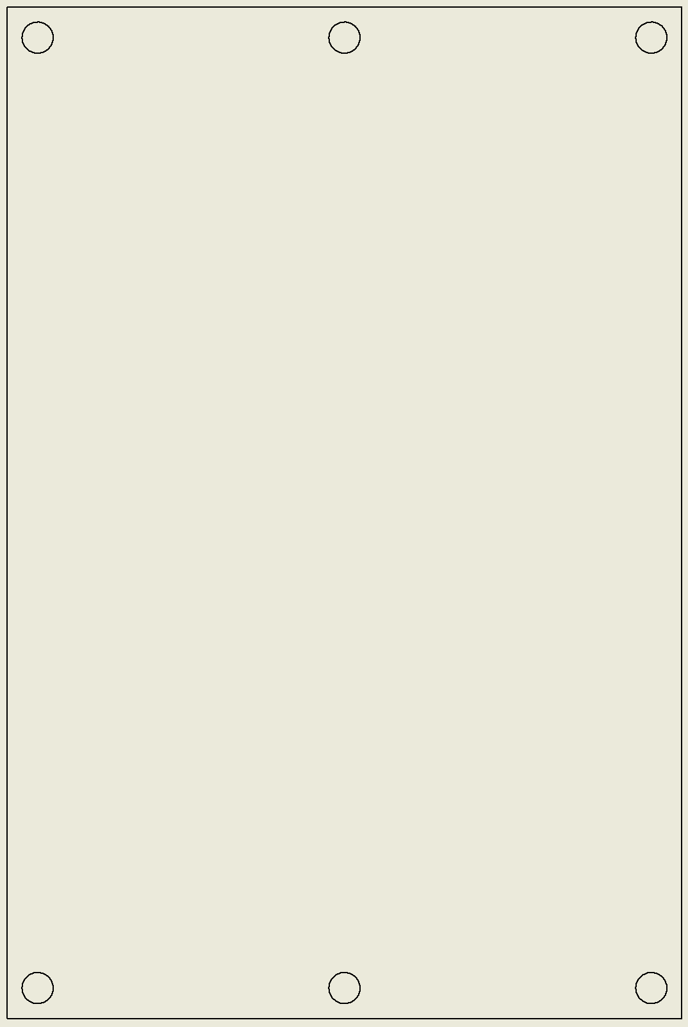
docs/assembly/L3-DIE.png
