openKolibri/klais-16/docs/assembly/L3.png

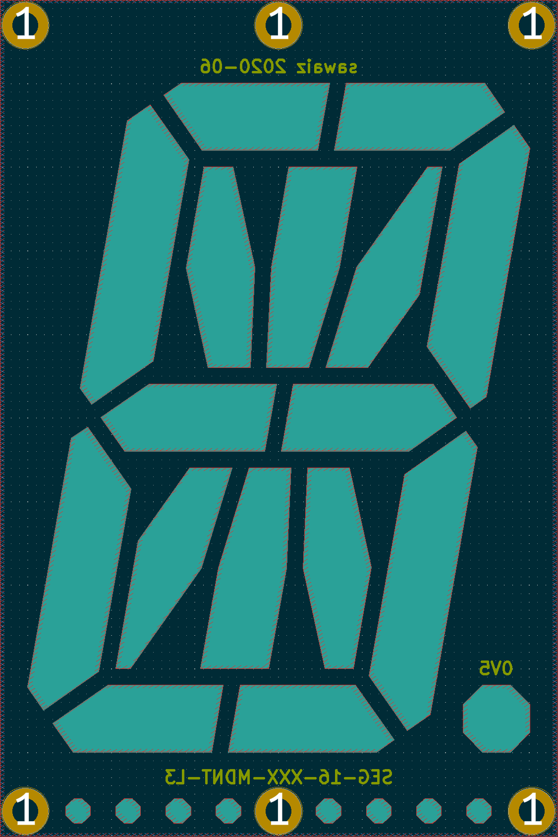
docs/assembly/L3.png
