openKolibri/klais-16/docs/mounting/M3x8Installed.jpg

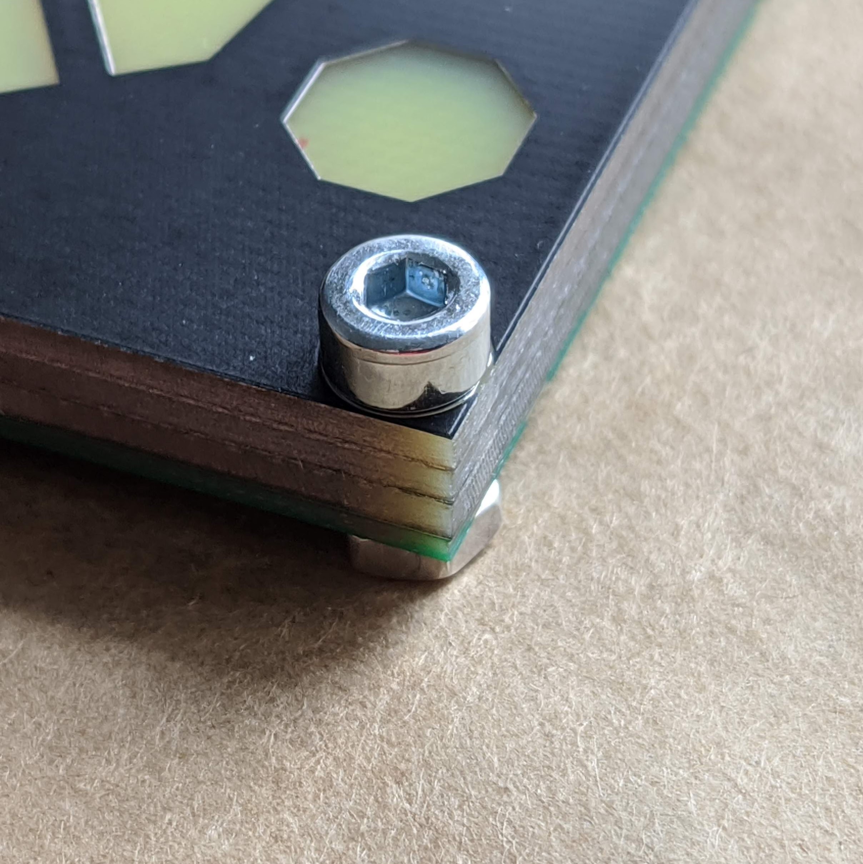
docs/mounting/M3x8Installed.jpg
