openKolibri/klais-16/pcb/SEG-16-XXX-XXXX-L0/SEG-16-XXX-XXXX-L0.pdf

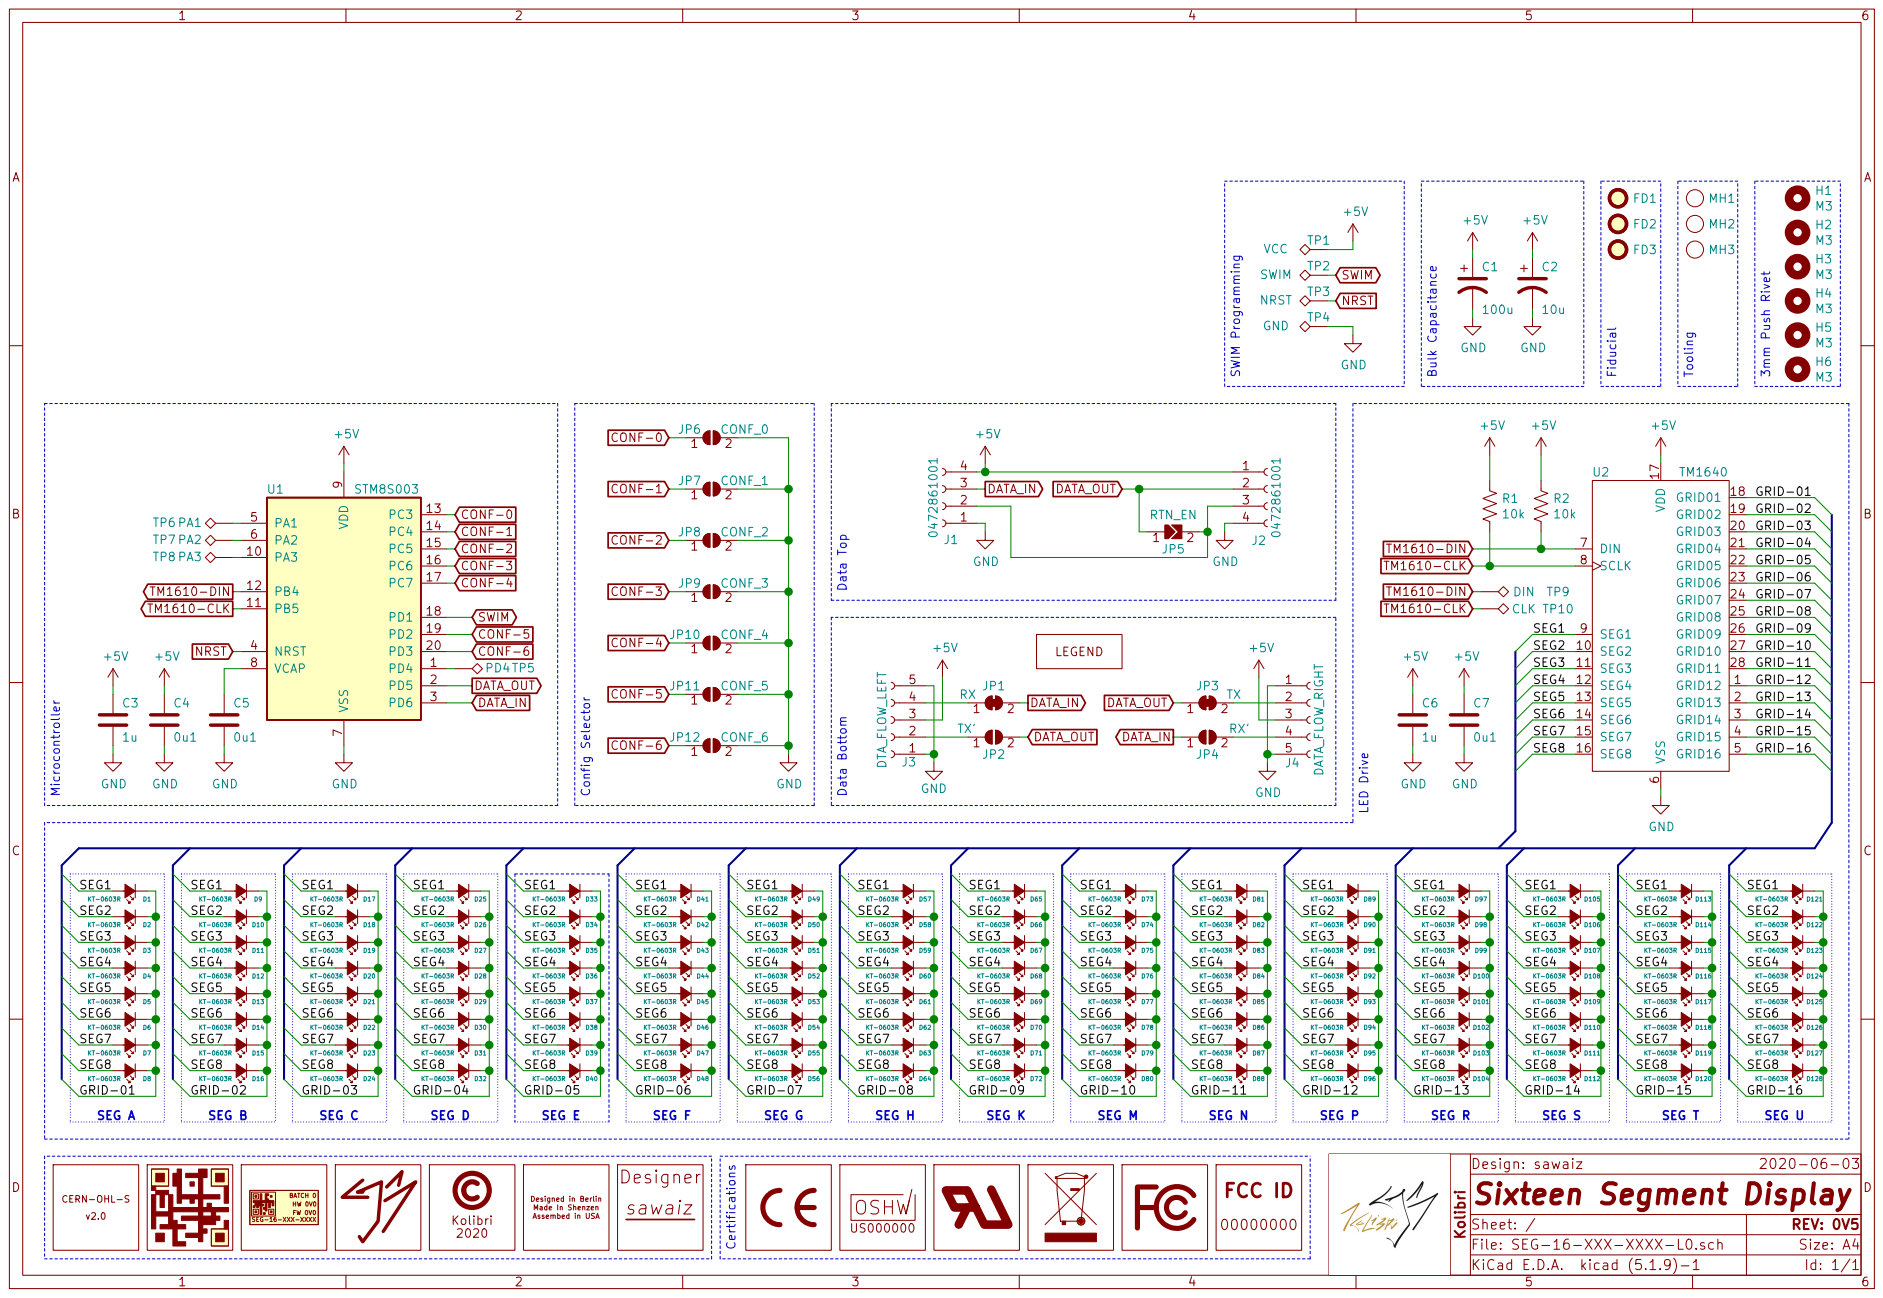
[picture p135: page 1]

6 DIN 7 SCLK 8 SEG1 9 U2 TM1640 +5V 00000000 FCC ID Designer

Id: 1/1 Sixteen Segment Display

BATCH 0 FW 0V0 HW 0V0 SEG-16-XXX-XXXX

Assembed in USA Designed in Berlin Made In Shenzen
