openKolibri/klais-16/docs/userGuide/toolsAndParts.jpg

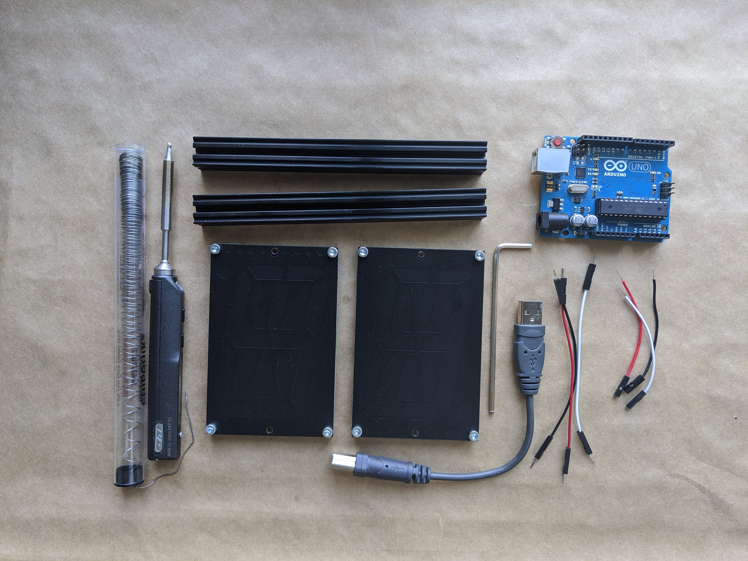
docs/userGuide/toolsAndParts.jpg
